twalker/3x5_tractyl/case/antoni-gaudi-Ca la Rosa_enhanced.webp

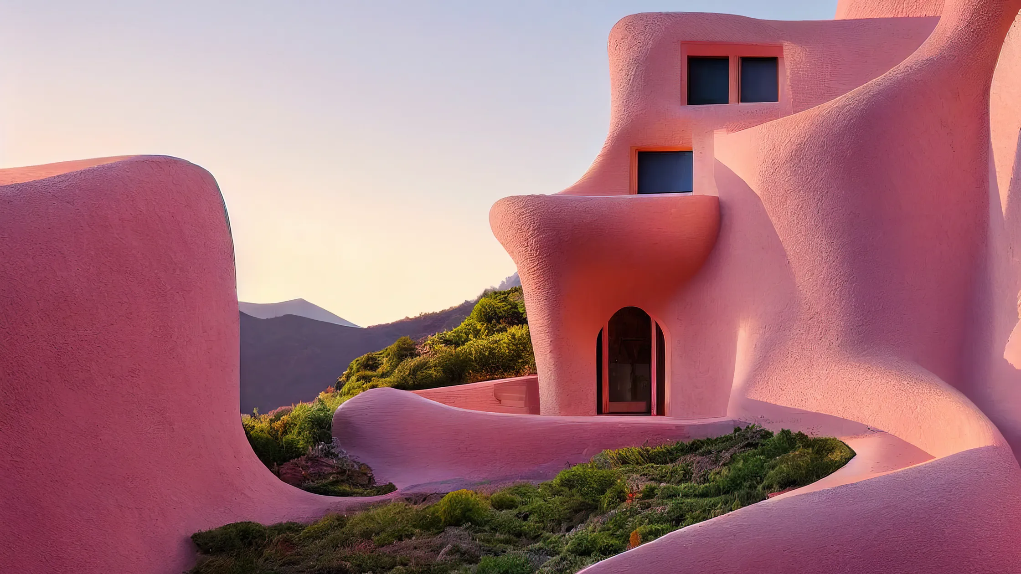
case/antoni-gaudi-Ca la Rosa_enhanced.webp
