twalker/3x5_tractyl/case/cosmos-design.png

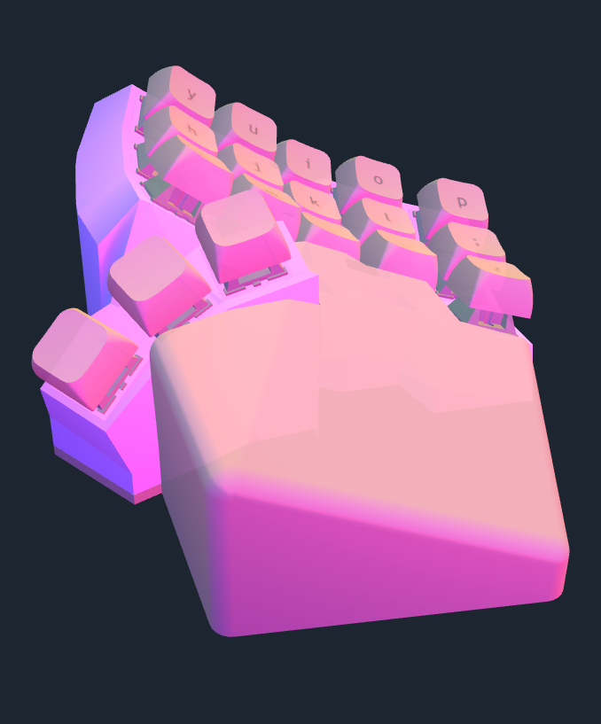
case/cosmos-design.png
