twalker/3x5_tractyl/case/orbital-in-slicer.png

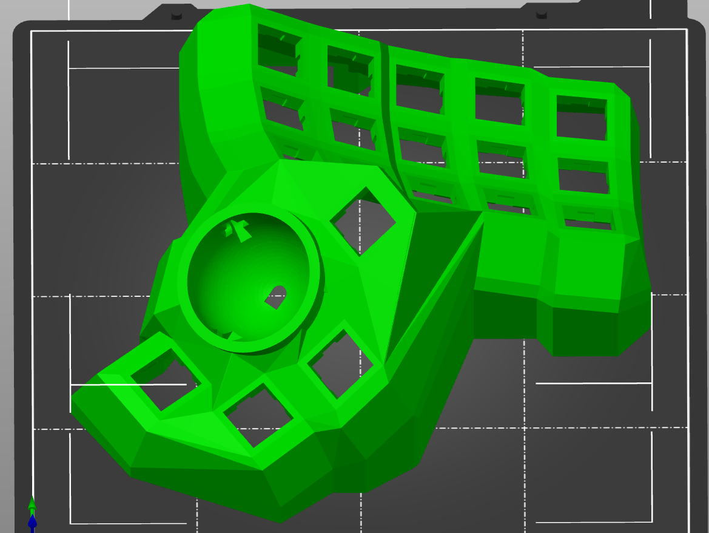
case/orbital-in-slicer.png
