twalker/3x5_tractyl/v2/3x5_tractyl-BothSidesRP2040_ce.png

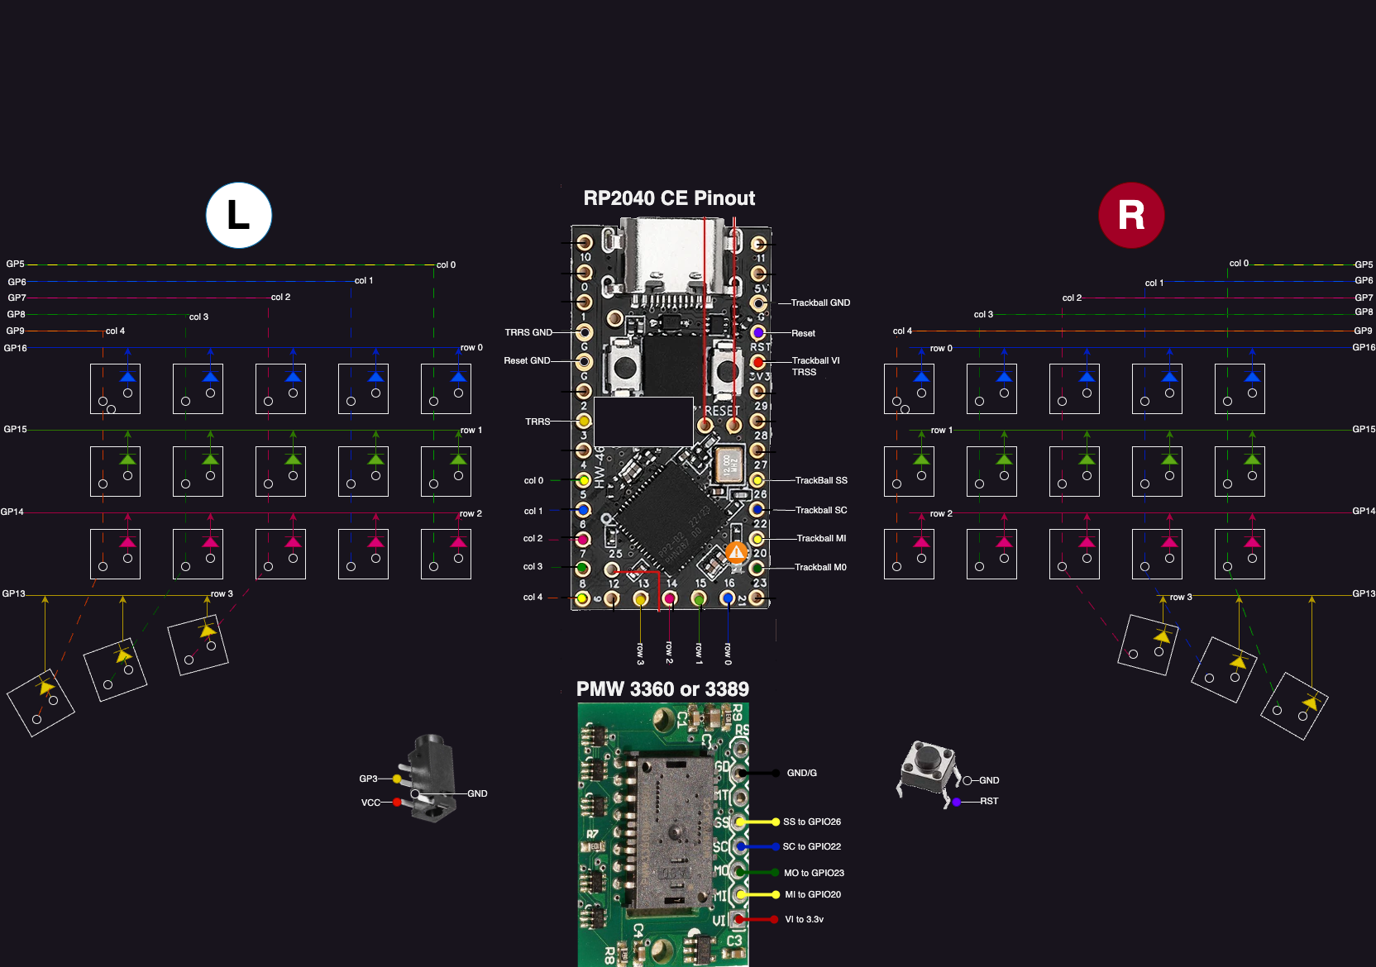
v2/3x5_tractyl-BothSidesRP2040_ce.png
