twalker/3x5_tractyl/v2/pmw3360_cleaned.jpg

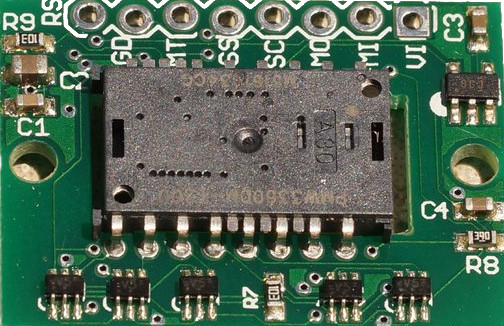
v2/pmw3360_cleaned.jpg
