twalker/3x5_tractyl/v2/Pro-Micro-RP2040-Mini-Development-Board-Dual-Core-Development-Board-Supports-Raspberry-Pi-Pico-MicroPython-4MB.jpg_.webp

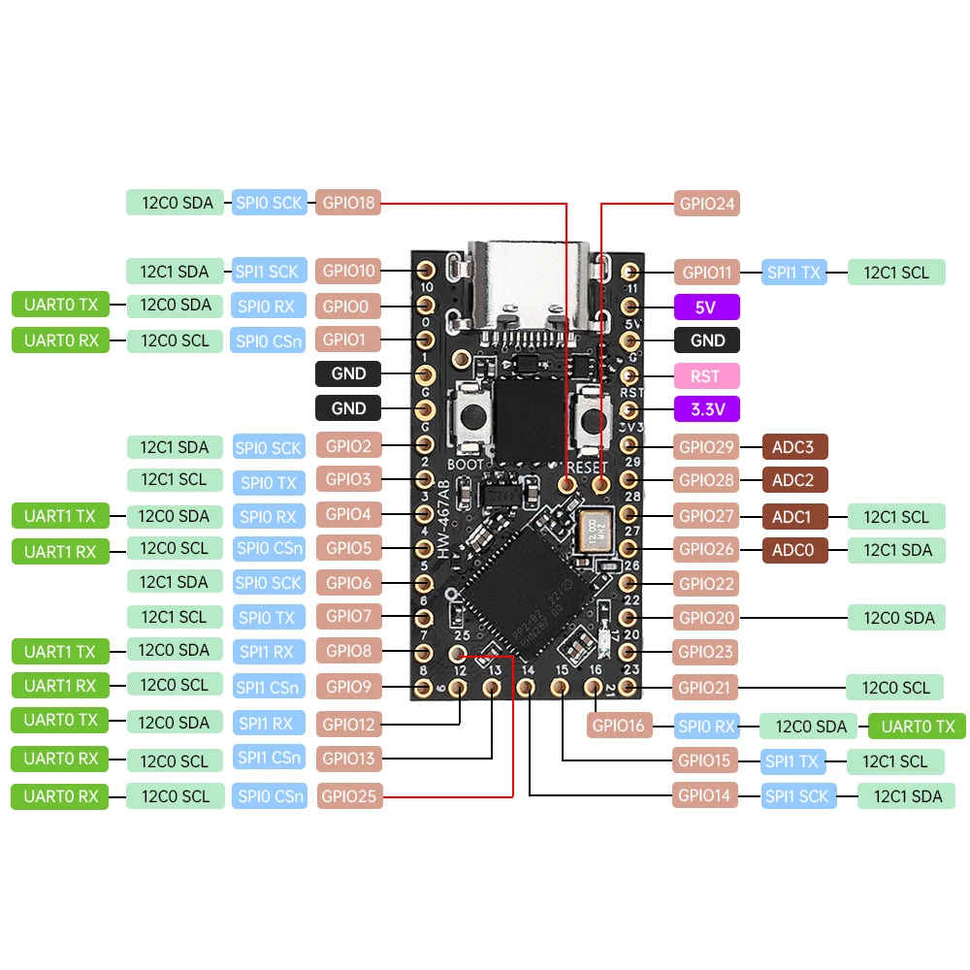
v2/Pro-Micro-RP2040-Mini-Development-Board-Dual-Core-Development-Board-Supports-Raspberry-Pi-Pico-MicroPython-4MB.jpg_.webp
