twalker/3x5_tractyl/v2/rp2040_ce.png

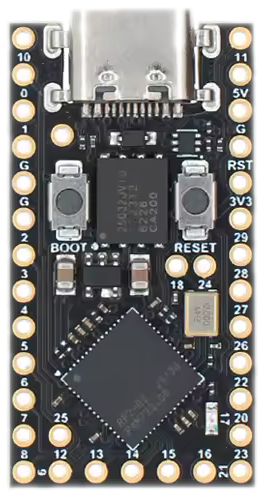
v2/rp2040_ce.png
