twalker/3x5_tractyl/v2/SpiralGalaxySKPCB.png

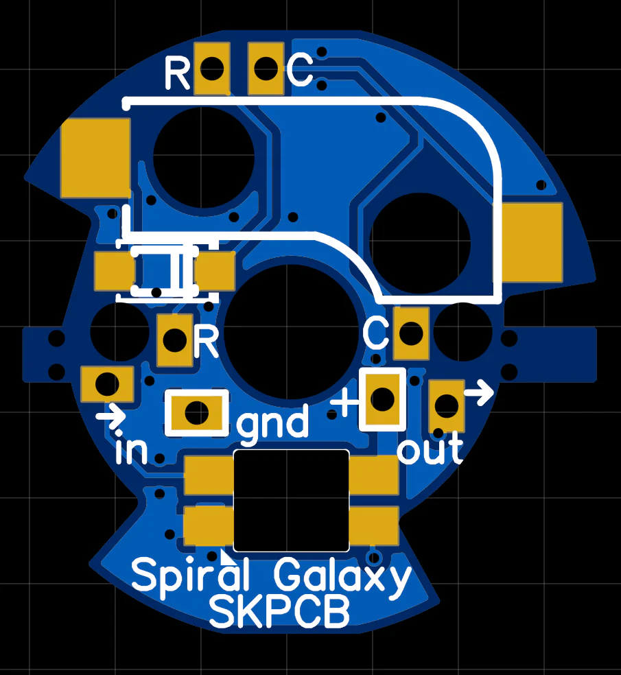
v2/SpiralGalaxySKPCB.png
