twalker/3x5_tractyl/v2_wireless/oled-positioning.png

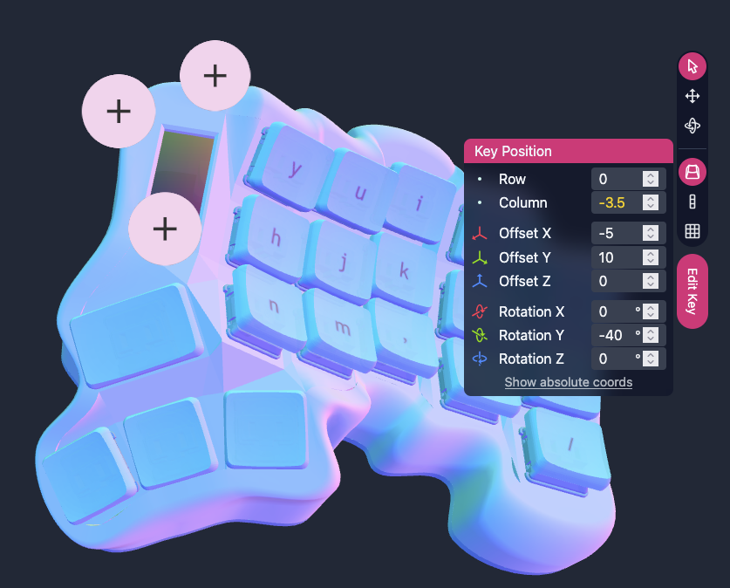
v2_wireless/oled-positioning.png
