twalker/3x5_tractyl/wiring-diagram/Elite-Pi_Pinout-Both-cleaned.png

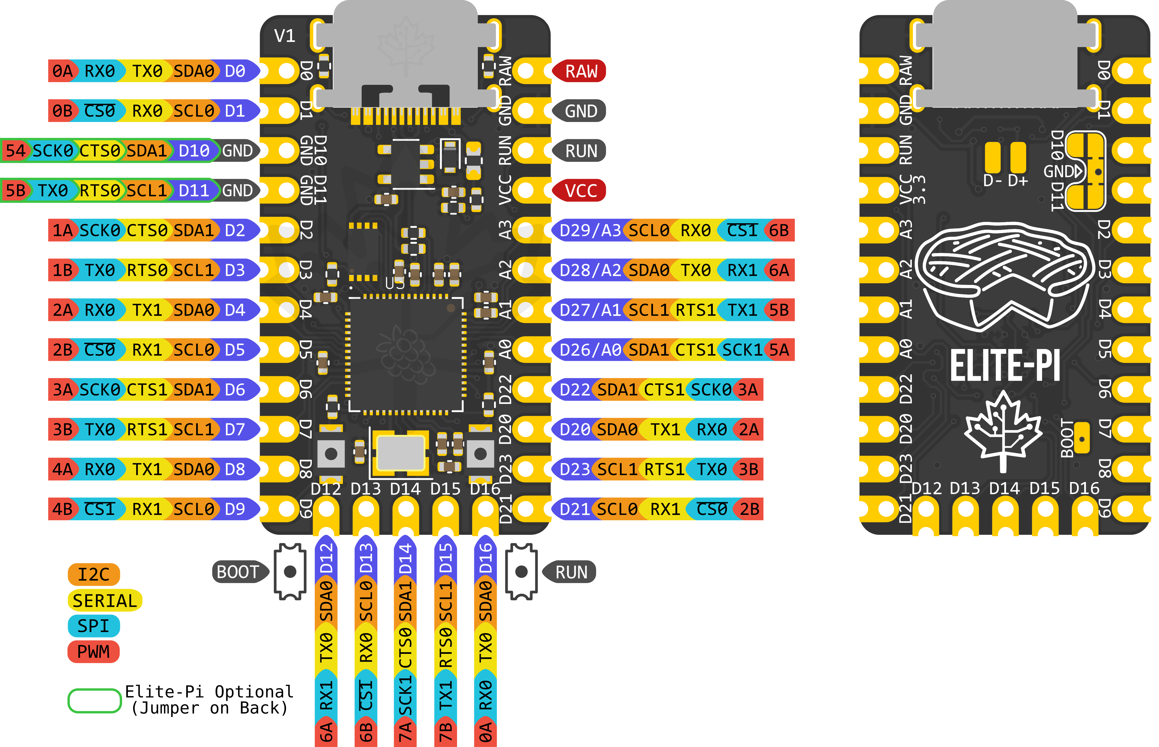
wiring-diagram/Elite-Pi_Pinout-Both-cleaned.png
