twalker/3x5_tractyl/wiring-diagram/Elite-Pi_Pinout-Top.png

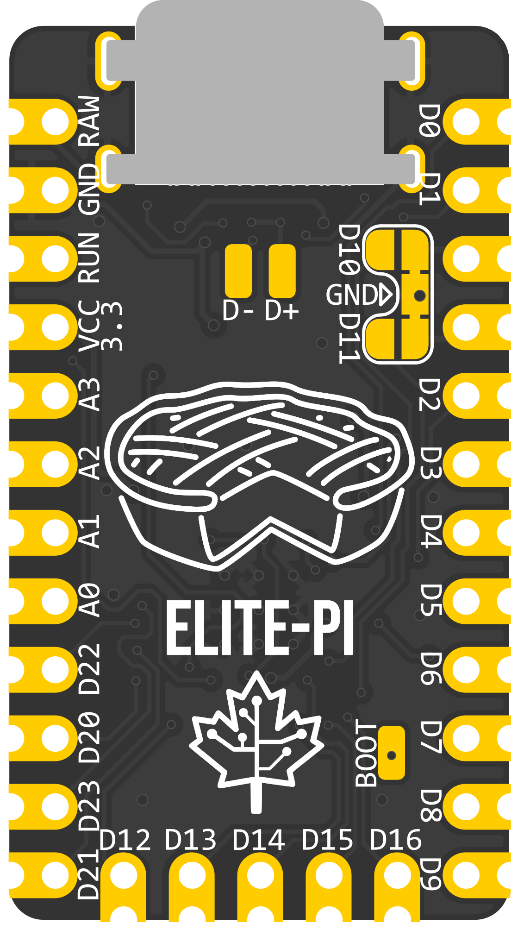
wiring-diagram/Elite-Pi_Pinout-Top.png
