twalker/3x5_tractyl/wiring-diagram/nice-view-pinout_cleaned.png

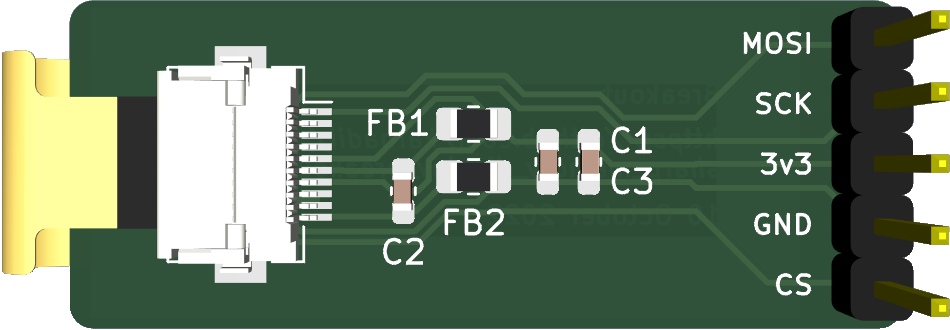
wiring-diagram/nice-view-pinout_cleaned.png
