twalker/3x5_tractyl/wiring-diagram/nice_nano_pinout-v2.png

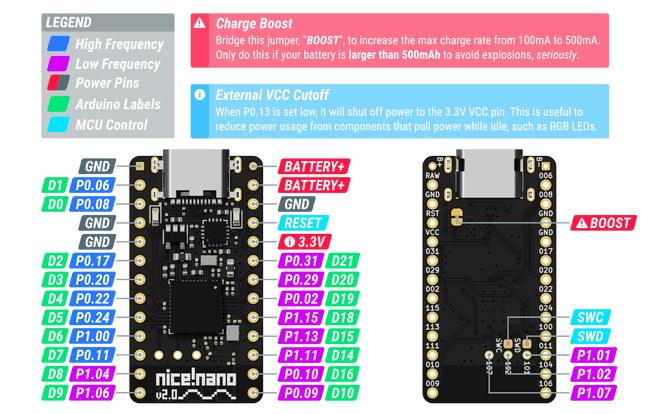
wiring-diagram/nice_nano_pinout-v2.png
