twalker/3x5_tractyl/wiring-diagram/pinout-advice.png

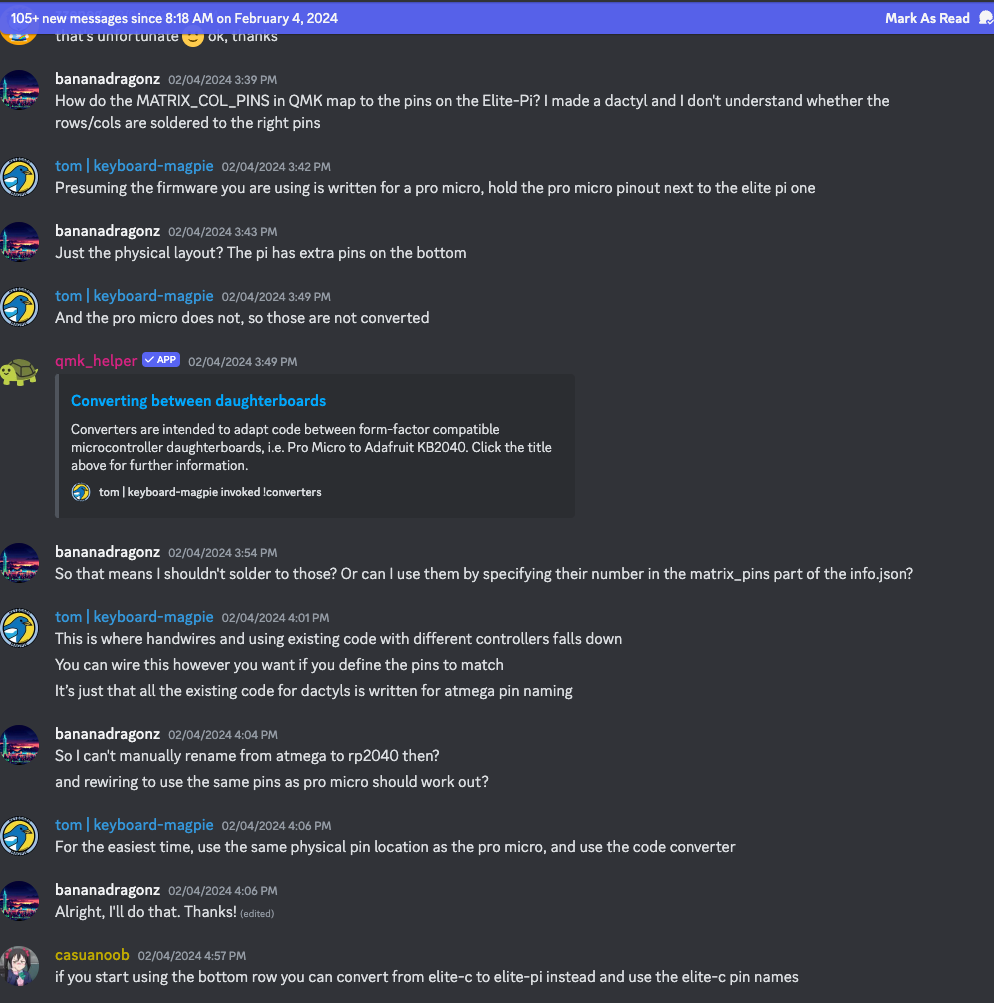
wiring-diagram/pinout-advice.png
