twalker/3x5_tractyl/wiring-diagram/promicro-pinout.png

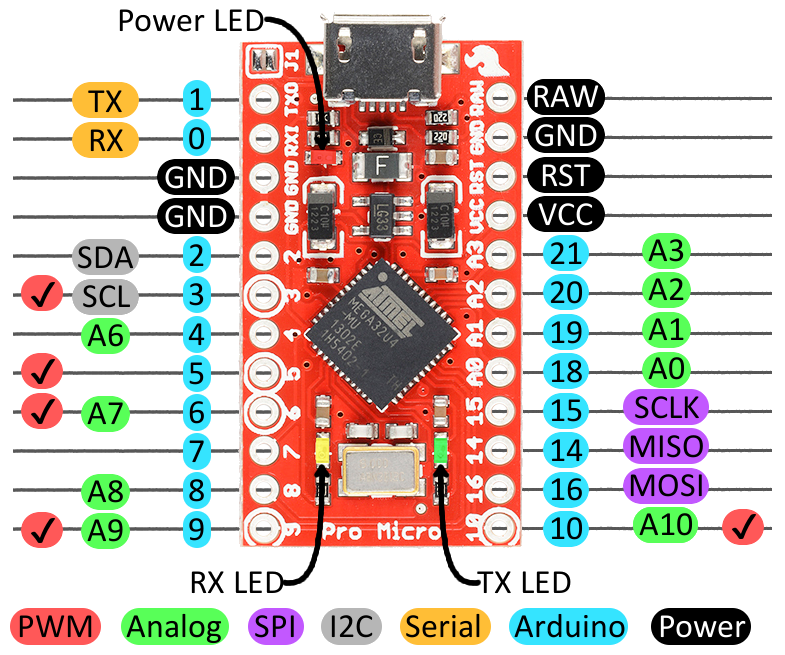
wiring-diagram/promicro-pinout.png
