twalker/3x5_tractyl/wiring-diagram/supermini-nrf52840-a-6-nice-nano-2-0-compatible-mcu-pinout.png

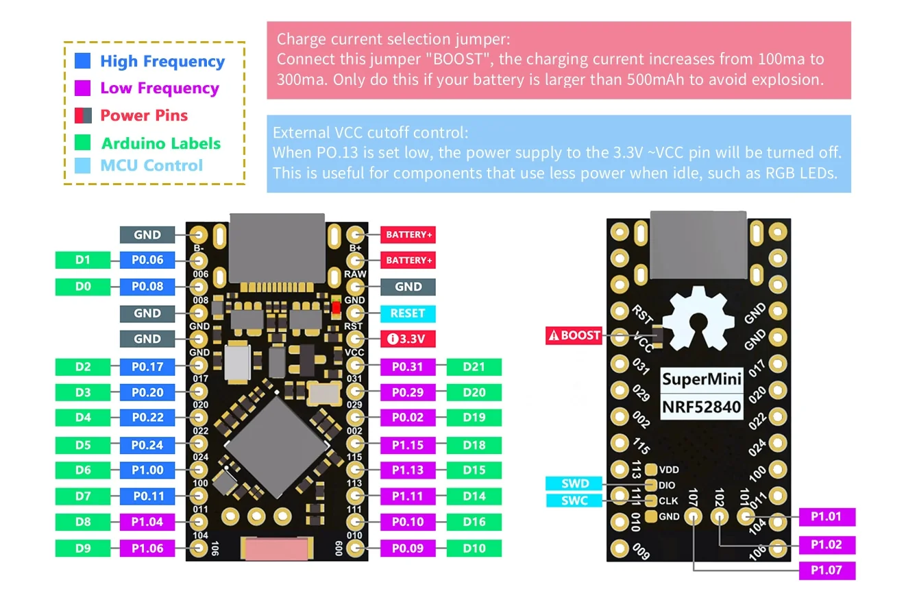
wiring-diagram/supermini-nrf52840-a-6-nice-nano-2-0-compatible-mcu-pinout.png
