twalker/3x5_tractyl/bill-of-materials.png

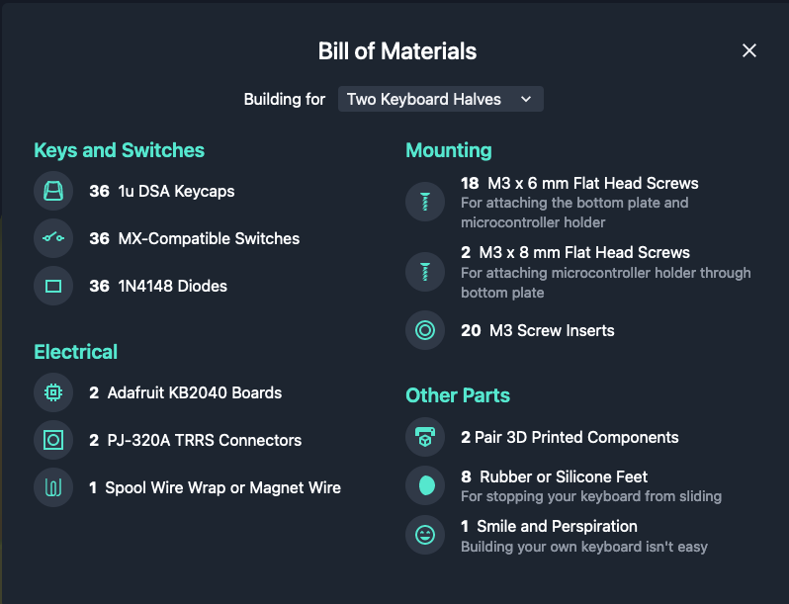
bill-of-materials.png
