twalker/3x5_tractyl/luca/luca_v2_hs_sm/luca_v2_hs_sm-plateright.stl

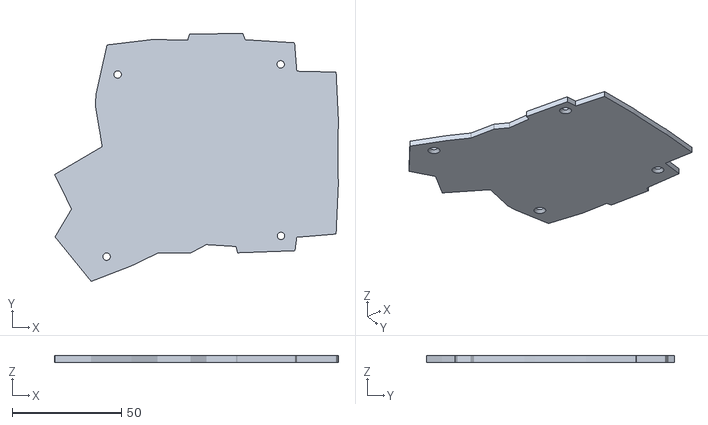
[picture p36: CAD file, 2026-05-09]
luca/luca_v2_hs_sm/luca_v2_hs_sm-plateright.stl
130.2 x 113.6 x 3.00
