twalker/3x5_tractyl/luca_v2.1_hs/luca_v2.1_hs_lg-holderright.stl

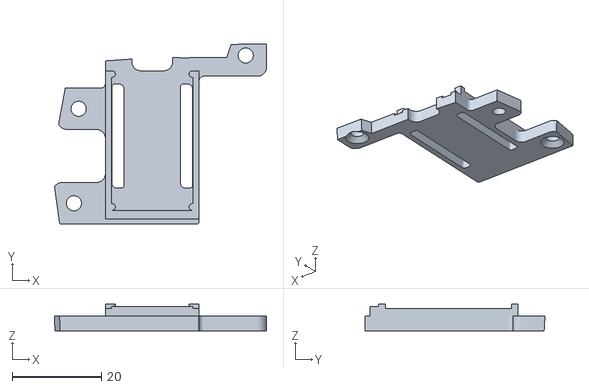
[picture p37: CAD file, 2026-05-09]
luca_v2.1_hs/luca_v2.1_hs_lg-holderright.stl
47.5 x 40.4 x 5.97
