twalker/3x5_tractyl/v2/cosmotylmt3v1-plateleft.stl

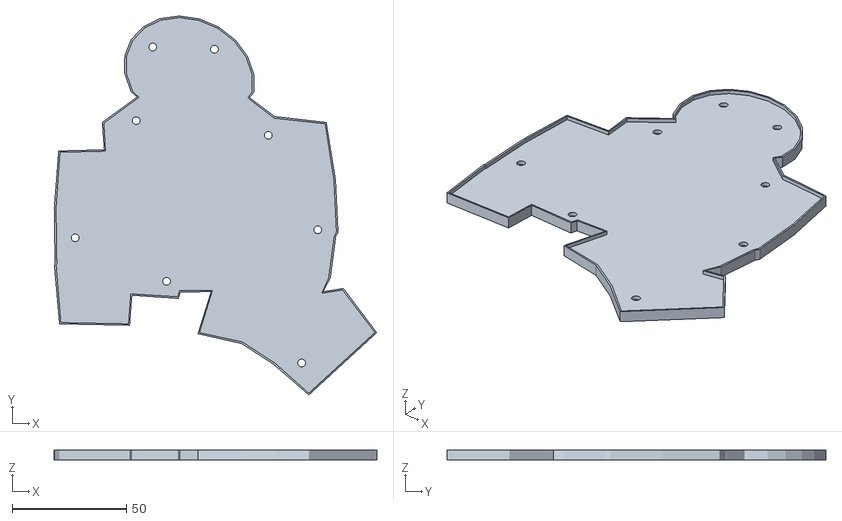
[picture p38: CAD file, 2024-12-28]
v2/cosmotylmt3v1-plateleft.stl
141.1 x 165.9 x 4.52
