twalker/3x5_tractyl/v2/costmos_choc_hotswap_v2/cosmos_choc_hotwap_v2.2-plateleft.stl

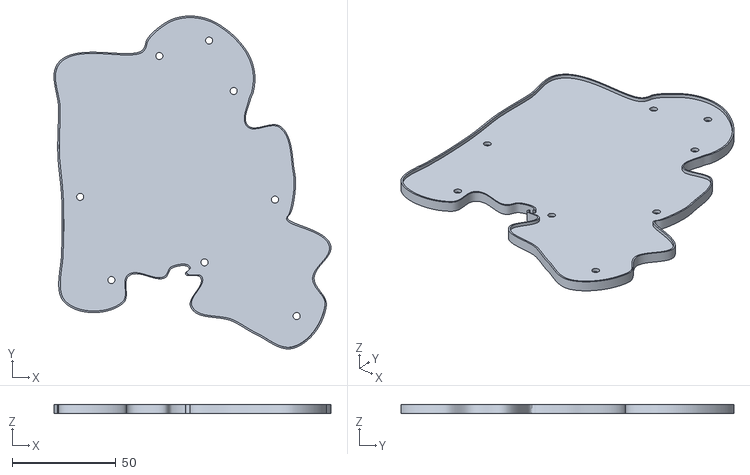
[picture p39: CAD file, 2024-12-28]
v2/costmos_choc_hotswap_v2/cosmos_choc_hotwap_v2.2-plateleft.stl
133.4 x 160.3 x 4.50
