twalker/3x5_tractyl/v2_wireless/cosmos_choc_hotwap_wireless_v2.5-holderright.stl

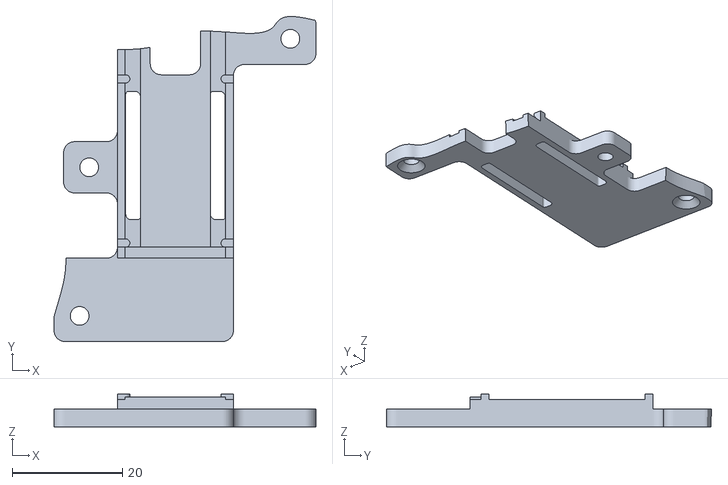
[picture p40: CAD file, 2025-02-22]
v2_wireless/cosmos_choc_hotwap_wireless_v2.5-holderright.stl
47.5 x 58.9 x 5.97
