twalker/3x5_tractyl/wireless_thumb_v1/v1.4/clemenza-thumb_v1.4-plateleft.stl

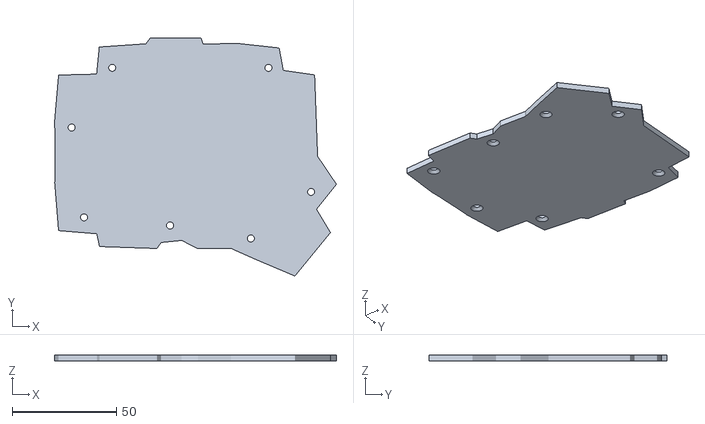
[picture p41: CAD file, 2026-05-09]
wireless_thumb_v1/v1.4/clemenza-thumb_v1.4-plateleft.stl
135.5 x 114.4 x 3.00
