twalker/3x5_tractyl/case/lowprocosmotyl2-noweb3-wristrest-longer.3mf

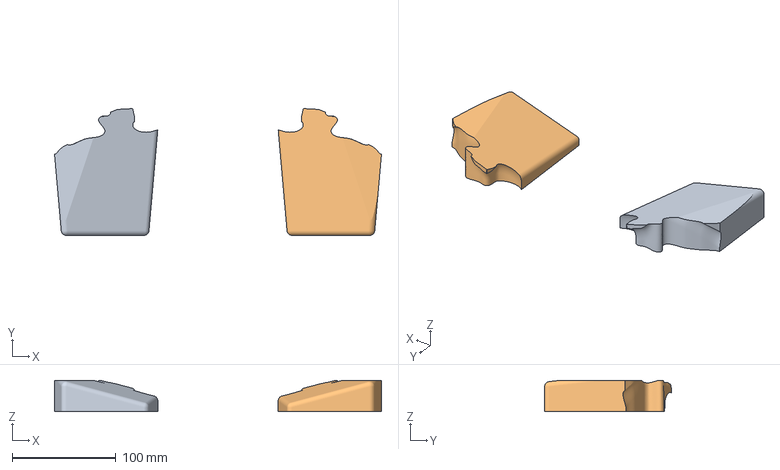
[picture p42: CAD file, 2024-06-30]
case/lowprocosmotyl2-noweb3-wristrest-longer.3mf
315.6 x 122.4 x 30.2 mm
lowprocosmotyl2-noweb3-wristrest-right.stl
lowprocosmotyl2-noweb3-wristrest-left.stl
