twalker/3x5_tractyl/clemenza-plus/clemenza-plus_v1-plateleft.stl

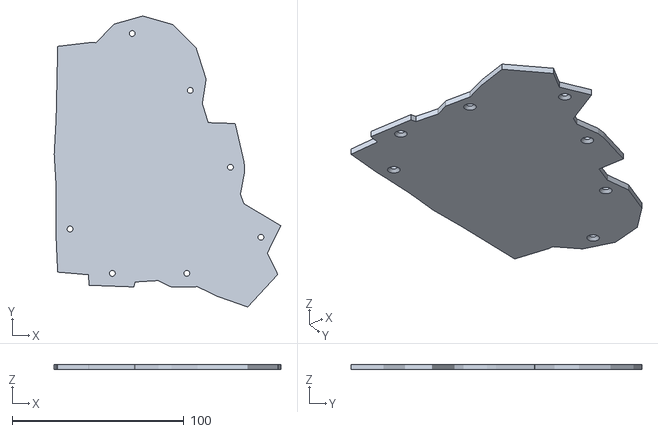
[picture p43: CAD file, 2026-05-09]
clemenza-plus/clemenza-plus_v1-plateleft.stl
132.1 x 169.6 x 3.00
