twalker/3x5_tractyl/luca/luca_v2_hs_lg/luca_v2_hs_lg.3mf

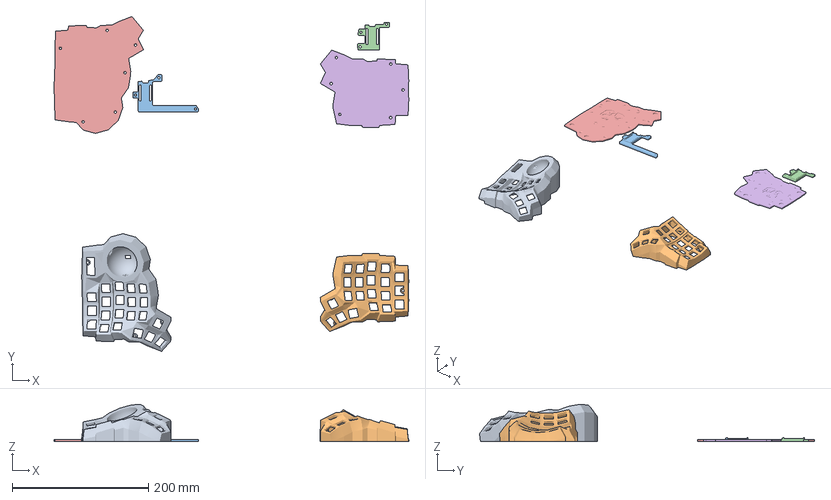
[picture p44: CAD file, 2026-05-09]
luca/luca_v2_hs_lg/luca_v2_hs_lg.3mf
521.2 x 492.3 x 54.9 mm
luca_v2_hs_lg-caseleft.stl
luca_v2_hs_lg-caseright.stl
luca_v2_hs_lg-holderleft.stl
luca_v2_hs_lg-holderright.stl
luca_v2_hs_lg-plateleft.stl
luca_v2_hs_lg-plateright.stl
