twalker/3x5_tractyl/luca/luca_v2_hs_sm/luca_v2_hs_sm-plateleft.stl

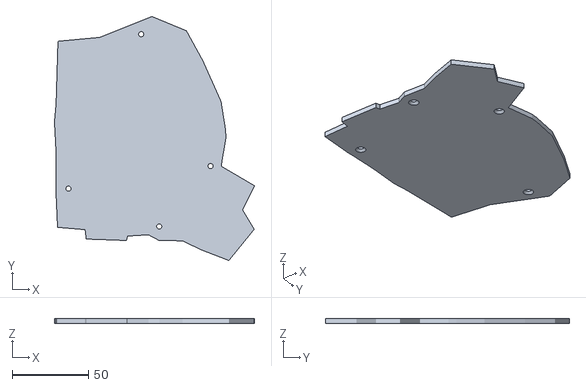
[picture p45: CAD file, 2026-05-09]
luca/luca_v2_hs_sm/luca_v2_hs_sm-plateleft.stl
131.1 x 159.9 x 3.00
