twalker/3x5_tractyl/v2/cosmos_choc_hotwap_v2.41/cosmos_choc_hotwap_v2.41-holderright.stl

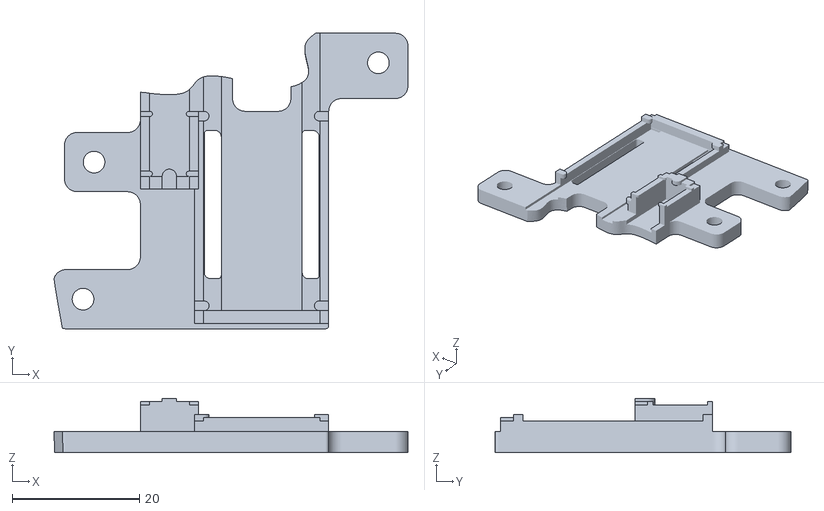
[picture p46: CAD file, 2025-01-20]
v2/cosmos_choc_hotwap_v2.41/cosmos_choc_hotwap_v2.41-holderright.stl
55.6 x 46.4 x 8.50
