twalker/3x5_tractyl/v2/cosmoskreedes_v1-holderleft.stl

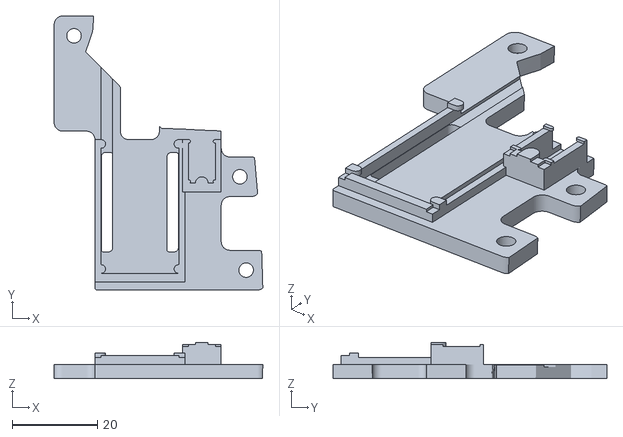
[picture p47: CAD file, 2024-12-28]
v2/cosmoskreedes_v1-holderleft.stl
48.9 x 64.1 x 8.50
