twalker/3x5_tractyl/v2/costmos_choc_hotswap_v2/cosmos_choc_hotwap_v2.2-holderleft.stl

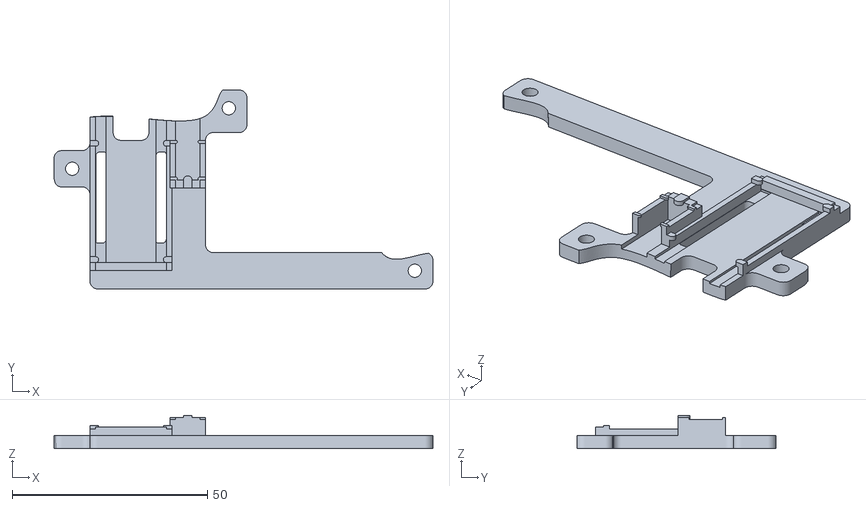
[picture p48: CAD file, 2024-12-28]
v2/costmos_choc_hotswap_v2/cosmos_choc_hotwap_v2.2-holderleft.stl
97.0 x 50.9 x 8.50
