twalker/3x5_tractyl/v2_wireless/cosmos_choc_hotwap_wireless_v2.5-holderleft.stl

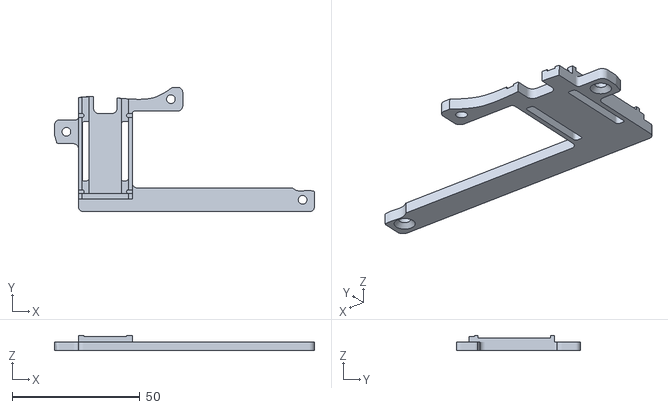
[picture p49: CAD file, 2025-02-22]
v2_wireless/cosmos_choc_hotwap_wireless_v2.5-holderleft.stl
101.6 x 48.6 x 5.97
