twalker/3x5_tractyl/case/lowprocosmotyl2-noweb-wristrests.3mf

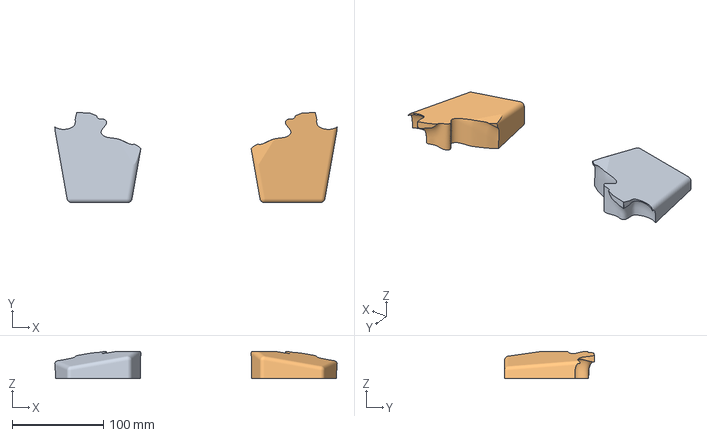
[picture p51: CAD file, 2024-06-30]
case/lowprocosmotyl2-noweb-wristrests.3mf
310.7 x 99.1 x 30.2 mm
lowprocosmotyl2-noweb-wristrest-left.stl
lowprocosmotyl2-noweb-wristrest-right.stl
