twalker/3x5_tractyl/clemenza-plus/clemenza-plus_v1-caseleft.stl

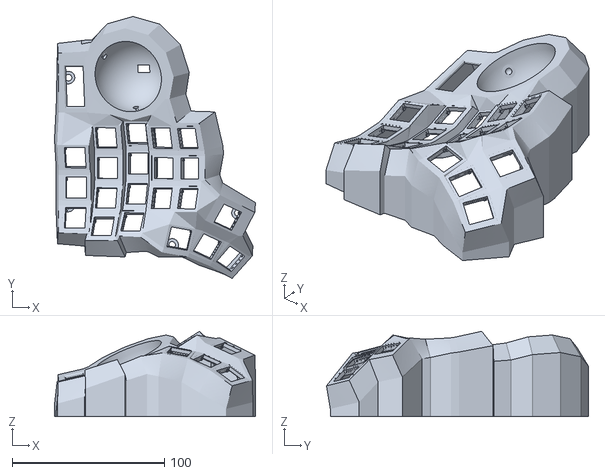
[picture p52: CAD file, 2026-05-09]
clemenza-plus/clemenza-plus_v1-caseleft.stl
132.1 x 172.1 x 56.1
