twalker/3x5_tractyl/luca/luca_v1.5-casetest.stl

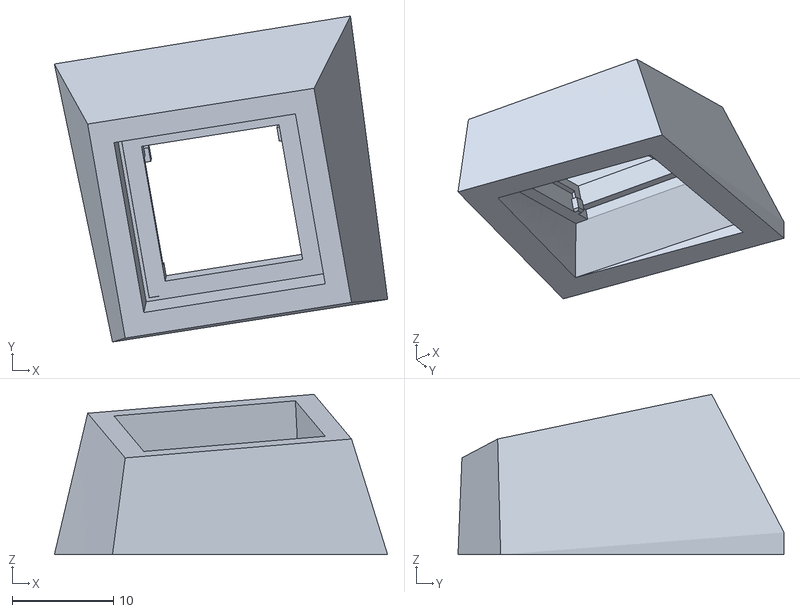
[picture p53: CAD file, 2026-05-09]
luca/luca_v1.5-casetest.stl
32.9 x 32.2 x 15.8
