twalker/3x5_tractyl/luca/luca_v2_hs_sm/luca_v2_hs_sm-caseright.stl

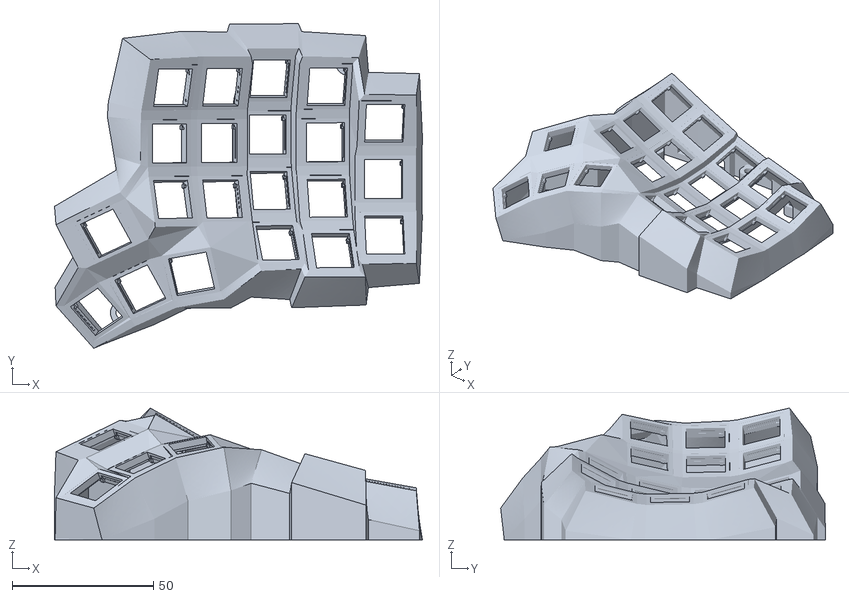
[picture p54: CAD file, 2026-05-09]
luca/luca_v2_hs_sm/luca_v2_hs_sm-caseright.stl
130.2 x 114.9 x 46.6
