twalker/3x5_tractyl/v2/cosmotylmt3v1-holderleft.stl

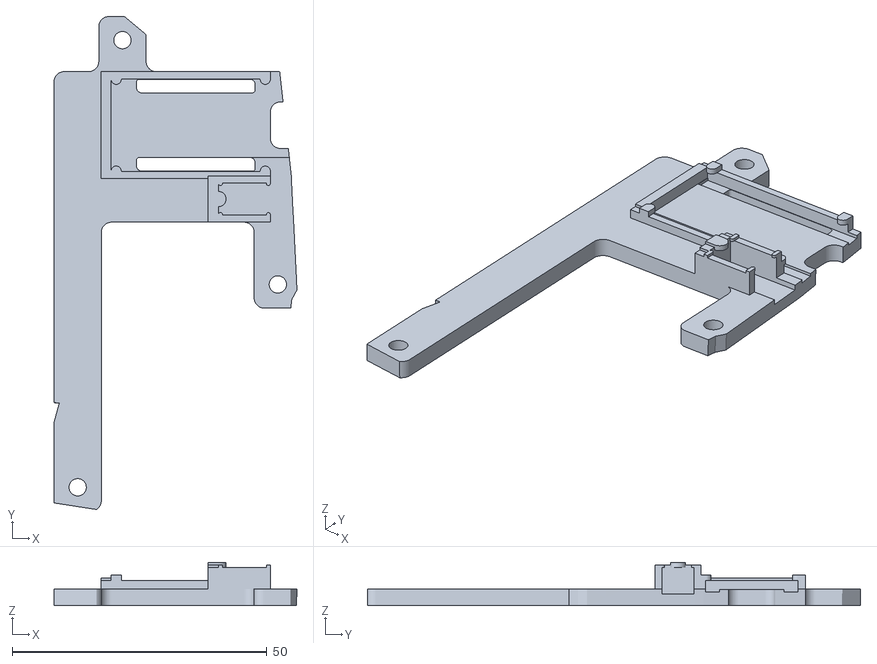
[picture p55: CAD file, 2024-12-28]
v2/cosmotylmt3v1-holderleft.stl
47.7 x 96.8 x 8.50
