twalker/3x5_tractyl/v2/costmos_choc_hotswap_v2/cosmos_choc_hotwap_v2.2-holderright.stl

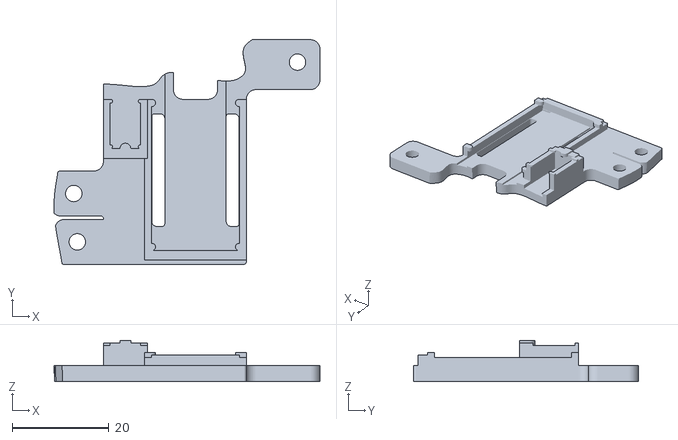
[picture p56: CAD file, 2024-12-28]
v2/costmos_choc_hotswap_v2/cosmos_choc_hotwap_v2.2-holderright.stl
55.0 x 46.5 x 8.50
