twalker/3x5_tractyl/v2_wireless/cosmos_choc_hotwap_wireless_v2.5-plateleft.stl

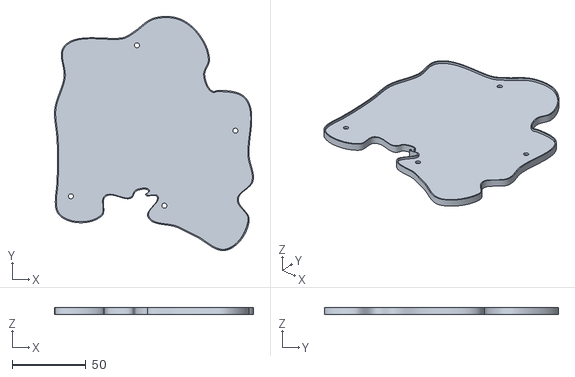
[picture p57: CAD file, 2025-02-22]
v2_wireless/cosmos_choc_hotwap_wireless_v2.5-plateleft.stl
134.6 x 158.4 x 4.50
