twalker/3x5_tractyl/wireless_thumb_v1/v1.4/clemenza-thumb_v1.4-plateright.stl

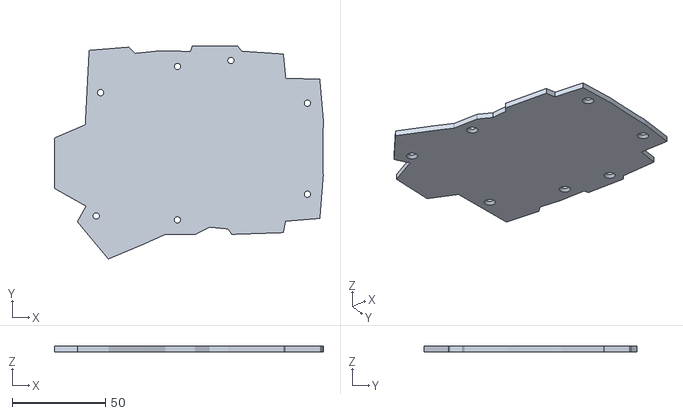
[picture p58: CAD file, 2026-05-09]
wireless_thumb_v1/v1.4/clemenza-thumb_v1.4-plateright.stl
144.4 x 114.4 x 3.00
