twalker/3x5_tractyl/case/lowprocosmotyl2-wristrest-left.stl

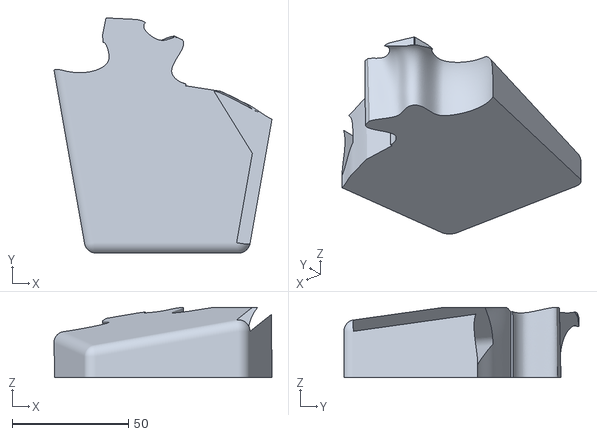
[picture p59: CAD file, 2024-06-30]
case/lowprocosmotyl2-wristrest-left.stl
93.6 x 101.0 x 30.2
