twalker/3x5_tractyl/clemenza-plus/clemenza-plus_v1.3mf

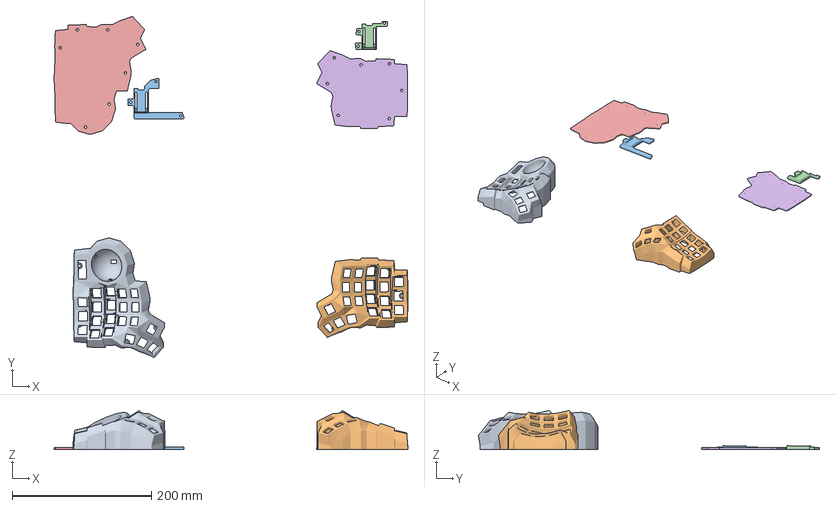
[picture p60: CAD file, 2026-05-09]
clemenza-plus/clemenza-plus_v1.3mf
508.7 x 490.3 x 56.1 mm
clemenza-plus_v1-caseleft.stl
clemenza-plus_v1-caseright.stl
clemenza-plus_v1-holderleft.stl
clemenza-plus_v1-holderright.stl
clemenza-plus_v1-plateleft.stl
clemenza-plus_v1-plateright.stl
