twalker/3x5_tractyl/luca/luca_v2_hs_sm/luca_v2_hs_sm-caseleft.stl

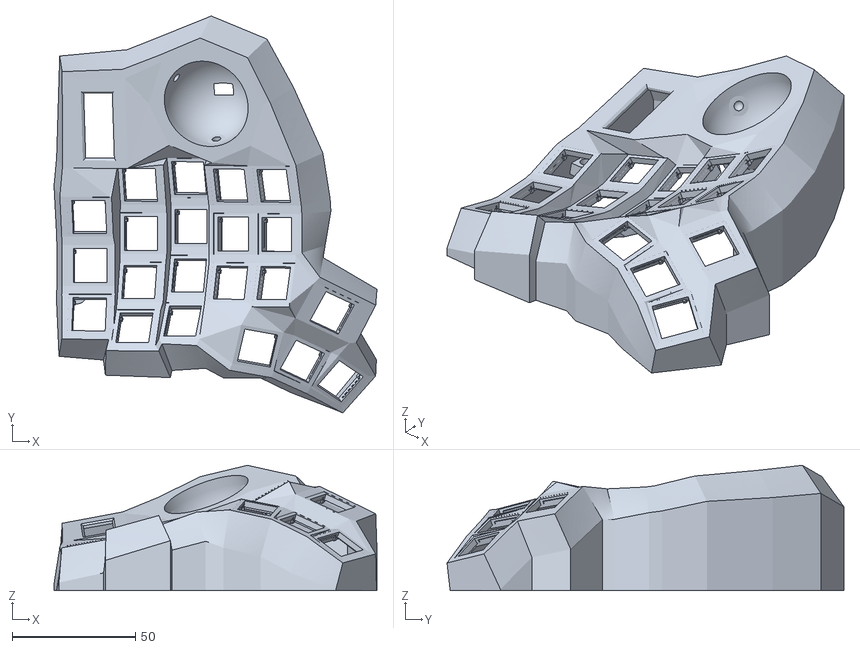
[picture p61: CAD file, 2026-05-09]
luca/luca_v2_hs_sm/luca_v2_hs_sm-caseleft.stl
131.1 x 161.2 x 50.9
