twalker/3x5_tractyl/v2/cosmoskreedes_v1-plateright.stl

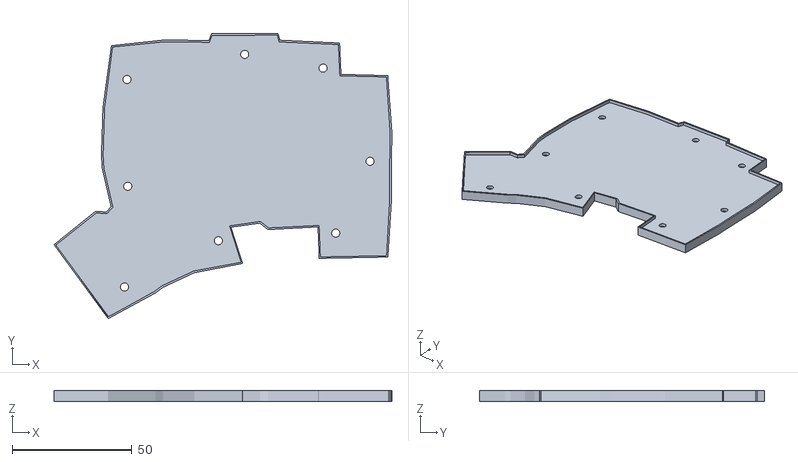
[picture p62: CAD file, 2024-12-28]
v2/cosmoskreedes_v1-plateright.stl
140.9 x 118.9 x 4.50
