twalker/3x5_tractyl/wireless_thumb_v1/v1.4/clemenza-thumb_v1.4-holderleft.stl

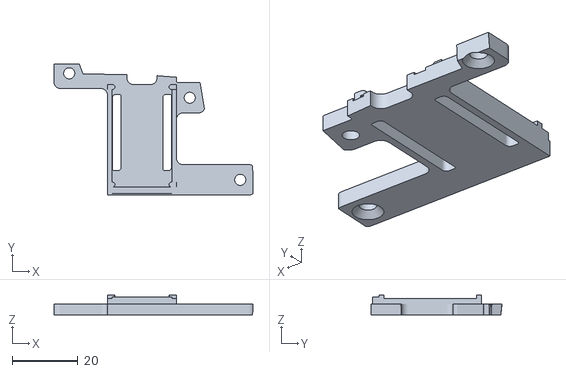
[picture p63: CAD file, 2026-05-09]
wireless_thumb_v1/v1.4/clemenza-thumb_v1.4-holderleft.stl
60.7 x 40.0 x 5.97
