twalker/3x5_tractyl/case/lowprocosmotyl2-holder-left.stl

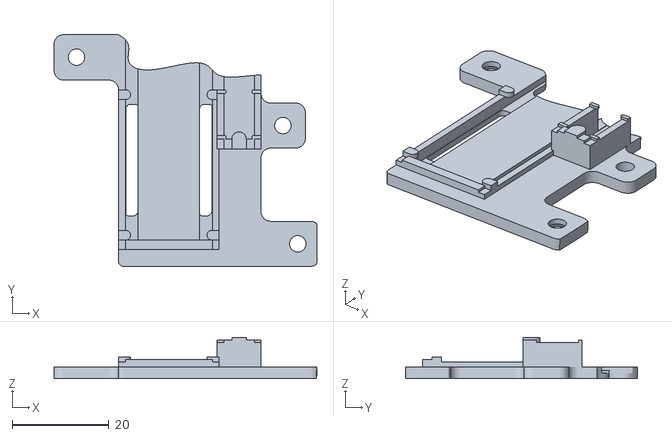
[picture p64: CAD file, 2024-06-30]
case/lowprocosmotyl2-holder-left.stl
54.3 x 47.8 x 8.50
