twalker/3x5_tractyl/luca/luca_v2_hs_lg/luca_v2_hs_lg-plateright.stl

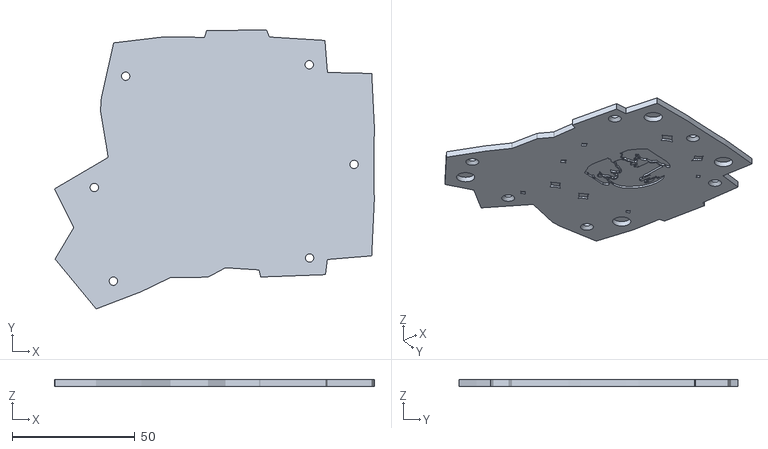
[picture p65: CAD file, 2026-05-09]
luca/luca_v2_hs_lg/luca_v2_hs_lg-plateright.stl
130.2 x 113.5 x 3.00
