twalker/3x5_tractyl/luca/luca_v2_hs_sm/luca_v2_hs_sm-holderright.stl

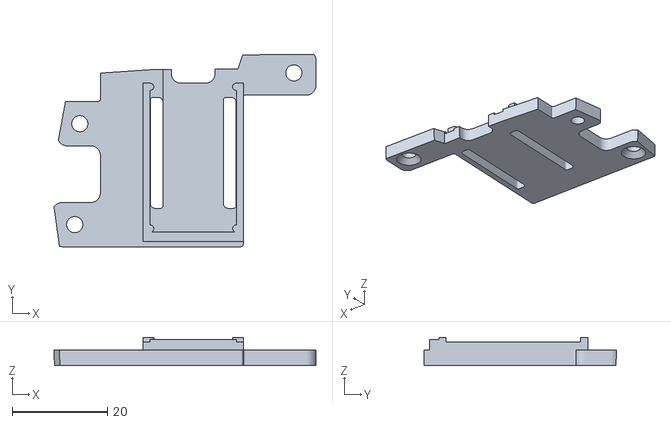
[picture p66: CAD file, 2026-05-09]
luca/luca_v2_hs_sm/luca_v2_hs_sm-holderright.stl
55.0 x 40.4 x 5.97
