twalker/3x5_tractyl/luca_v2.1_hs/luca_v2.1_hs_lg-caseright.stl

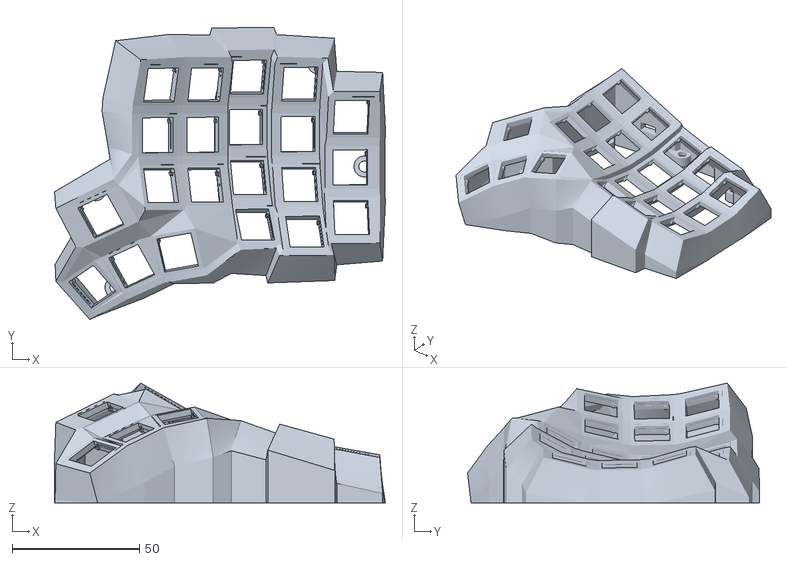
[picture p67: CAD file, 2026-05-09]
luca_v2.1_hs/luca_v2.1_hs_lg-caseright.stl
130.2 x 114.9 x 47.1
