twalker/3x5_tractyl/v2/cosmotylmt3v1-wristrestright.stl

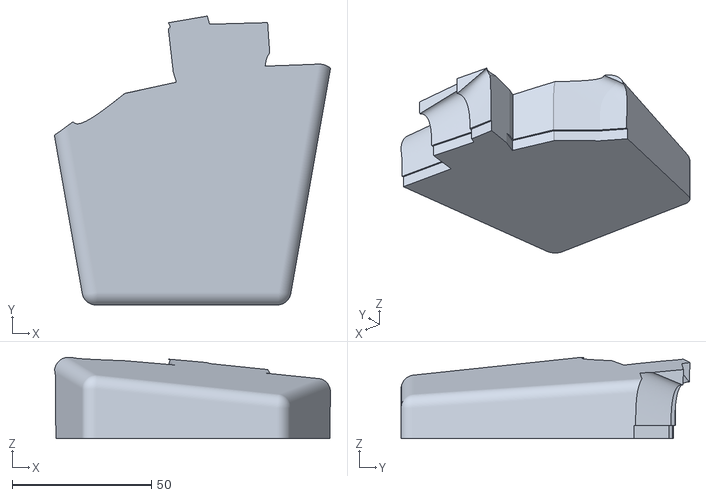
[picture p68: CAD file, 2024-12-28]
v2/cosmotylmt3v1-wristrestright.stl
99.2 x 103.9 x 29.1
