twalker/3x5_tractyl/wireless_thumb_v1/v1.4/clemenza-thumb_v1.4right.step

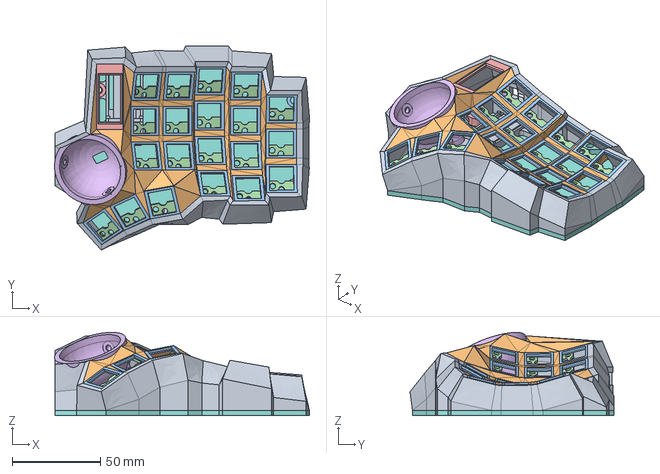
[picture p69: CAD file, 2026-05-09]
wireless_thumb_v1/v1.4/clemenza-thumb_v1.4right.step
144.7 x 115.8 x 47.2 mm
