twalker/3x5_tractyl/case/38mmTrackBallHolder.3mf

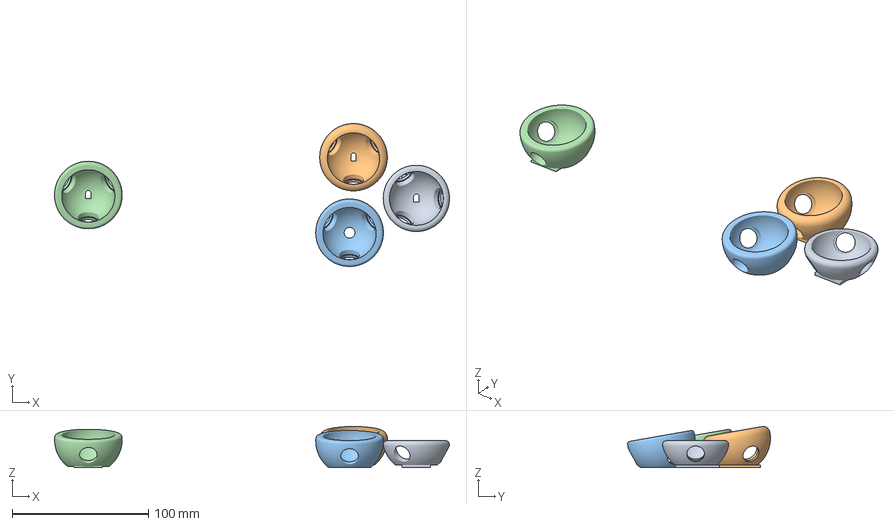
[picture p70: CAD file, 2024-06-30]
case/38mmTrackBallHolder.3mf
289.9 x 104.9 x 30.1 mm
38mmTrackBallHolder v15.stl
38mmTrackBallHolder v16.stl
Cup.stl
38mmTrackBallHolder v18.stl
