twalker/3x5_tractyl/clemenza-plus/clemenza-plus_v1-caseright.stl

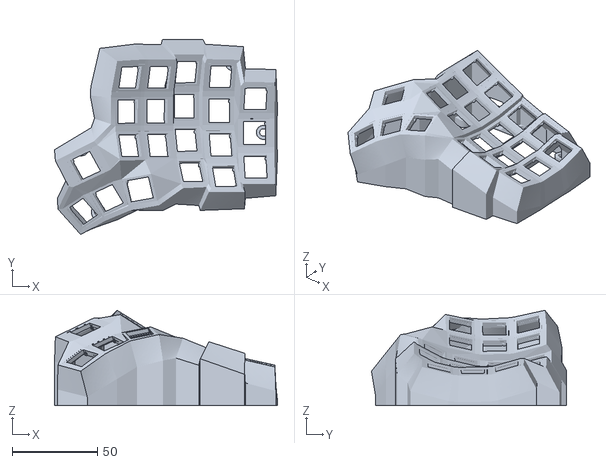
[picture p71: CAD file, 2026-05-09]
clemenza-plus/clemenza-plus_v1-caseright.stl
131.1 x 114.7 x 56.1
