twalker/3x5_tractyl/luca/luca_v2_hs_sm/luca_v2_hs_sm-holderleft.stl

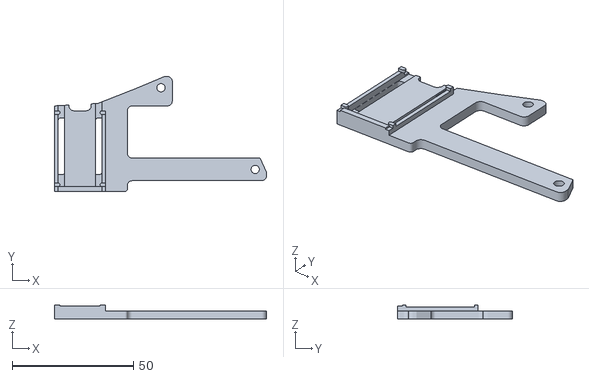
[picture p72: CAD file, 2026-05-09]
luca/luca_v2_hs_sm/luca_v2_hs_sm-holderleft.stl
87.3 x 47.4 x 5.97
