twalker/3x5_tractyl/wireless_thumb_v1/v1.4/clemenza-thumb_v1.4.3mf

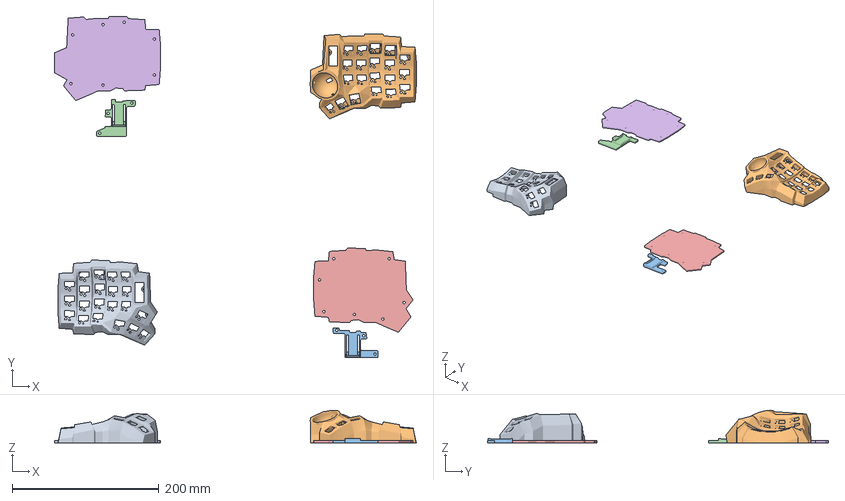
[picture p73: CAD file, 2026-05-09]
wireless_thumb_v1/v1.4/clemenza-thumb_v1.4.3mf
492.5 x 464.0 x 44.2 mm
clemenza-thumb_v1.4-caseleft.stl
clemenza-thumb_v1.4-caseright.stl
clemenza-thumb_v1.4-holderleft.stl
clemenza-thumb_v1.4-holderright.stl
clemenza-thumb_v1.4-plateleft.stl
clemenza-thumb_v1.4-plateright.stl
