twalker/3x5_tractyl/case/lowprocosmotyl2-noweb3-wristrest-left.stl

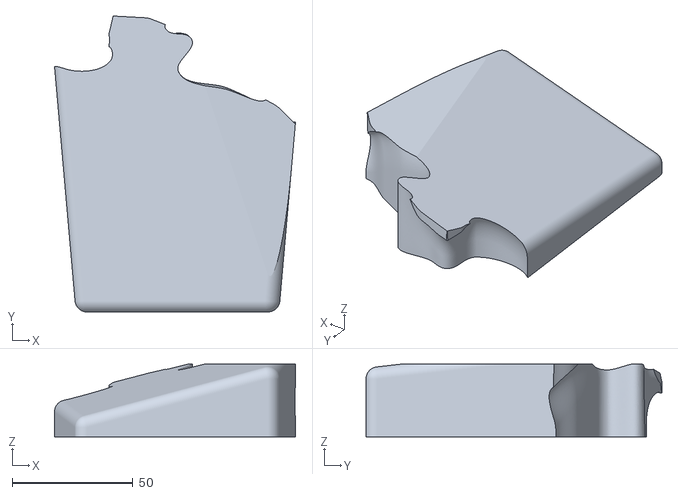
[picture p74: CAD file, 2024-06-30]
case/lowprocosmotyl2-noweb3-wristrest-left.stl
99.7 x 122.4 x 30.2
