twalker/3x5_tractyl/luca/luca_v2-plateleft.stl

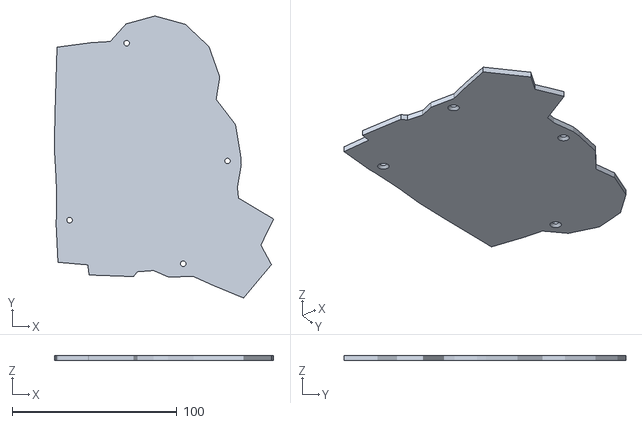
[picture p75: CAD file, 2026-05-09]
luca/luca_v2-plateleft.stl
133.0 x 171.1 x 3.00
