twalker/3x5_tractyl/v2/cosmoskreedes_v1-plateleft.stl

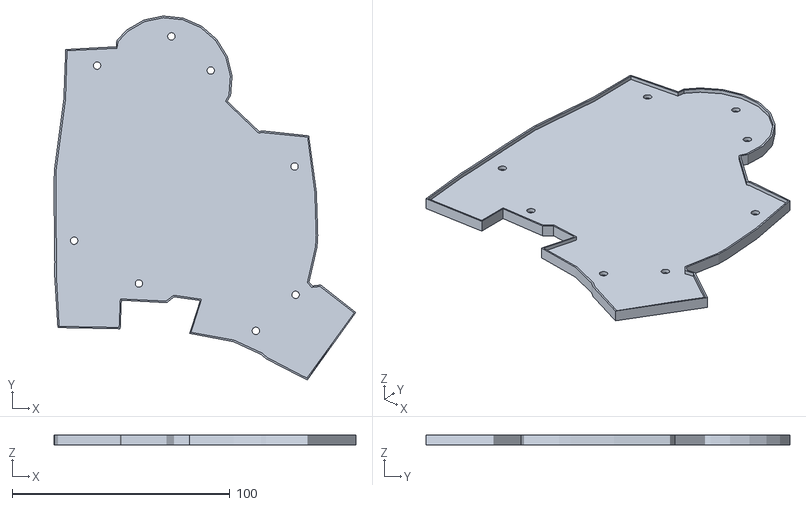
[picture p76: CAD file, 2024-12-28]
v2/cosmoskreedes_v1-plateleft.stl
138.6 x 167.3 x 4.52
