twalker/3x5_tractyl/wireless_thumb_v1/v1.4/clemenza-thumb_v1.4left.step

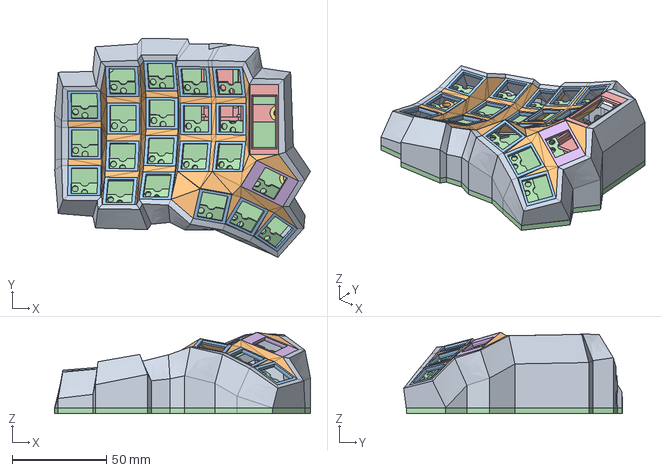
[picture p77: CAD file, 2026-05-09]
wireless_thumb_v1/v1.4/clemenza-thumb_v1.4left.step
135.5 x 115.8 x 43.1 mm
