twalker/3x5_tractyl/case/lowprocosmotyl2-noweb-parts.3mf

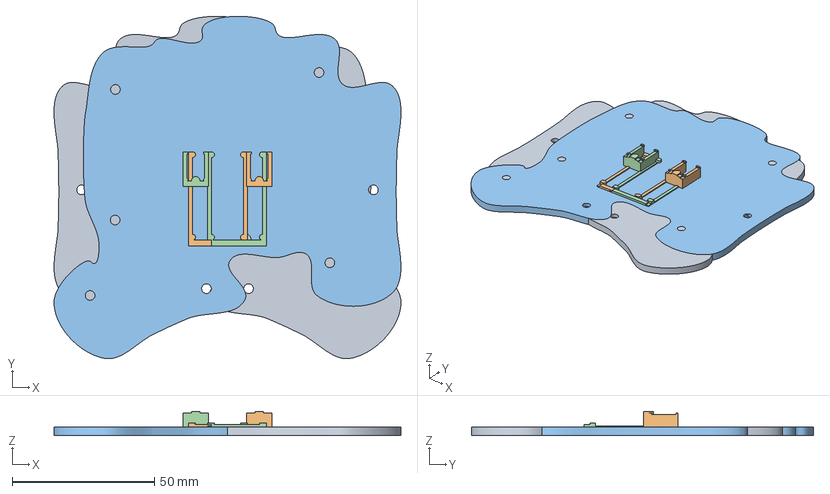
[picture p78: CAD file, 2024-06-30]
case/lowprocosmotyl2-noweb-parts.3mf
122.1 x 120.4 x 8.50 mm
lowprocosmotyl2-noweb-plate-left.stl
lowprocosmotyl2-noweb-holder-left.stl
lowprocosmotyl2-noweb-plate-right.stl
lowprocosmotyl2-noweb-holder-right.stl
