twalker/3x5_tractyl/v2/cosmos_choc_hotwap_v1.3mf

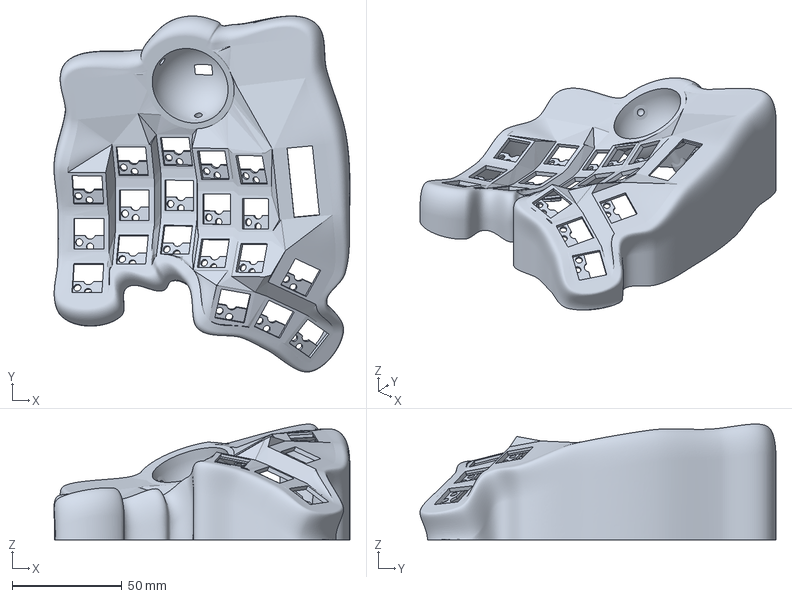
[picture p79: CAD file, 2024-12-28]
v2/cosmos_choc_hotwap_v1.3mf
134.8 x 162.2 x 52.8 mm
