twalker/3x5_tractyl/luca/luca_v2-holderright.stl

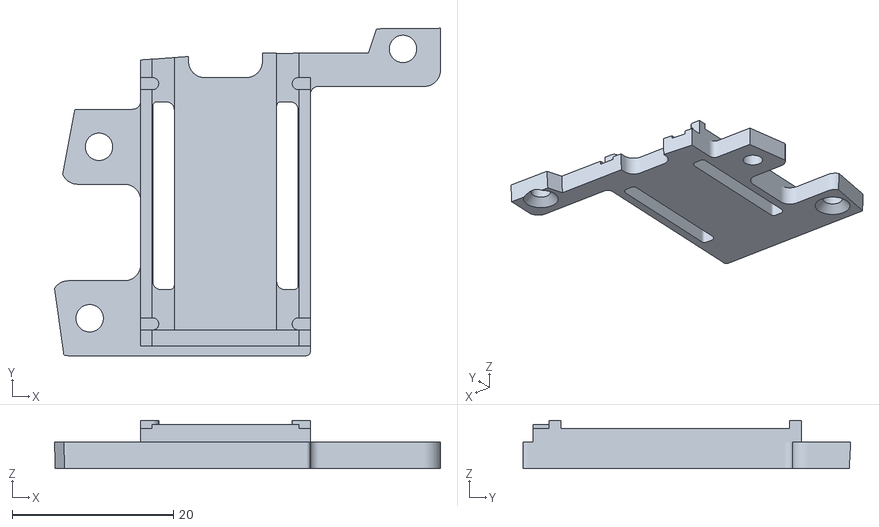
[picture p81: CAD file, 2026-05-09]
luca/luca_v2-holderright.stl
47.9 x 40.6 x 5.97
