twalker/3x5_tractyl/v2/cosmotylmt3v1-holderright.stl

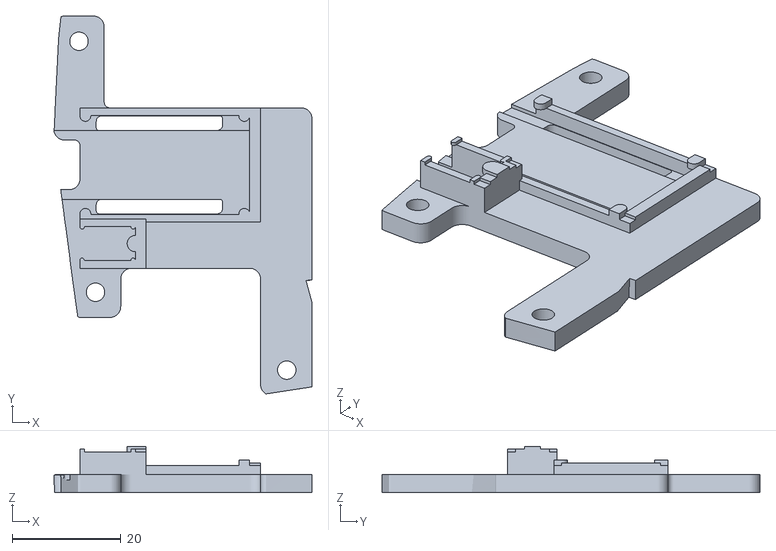
[picture p82: CAD file, 2024-12-28]
v2/cosmotylmt3v1-holderright.stl
47.5 x 69.6 x 8.50
