twalker/3x5_tractyl/case/trackball_holder.step

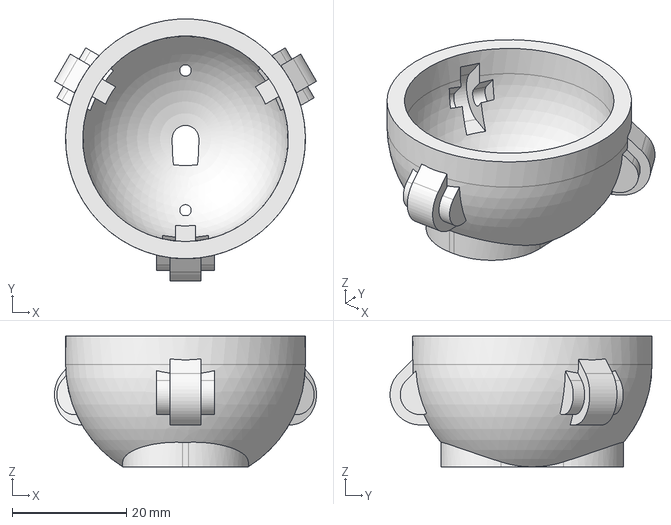
[picture p83: CAD file, 2024-06-30]
case/trackball_holder.step
45.9 x 45.9 x 22.9 mm
