twalker/3x5_tractyl/v2/cosmoskreedes_v1.3mf

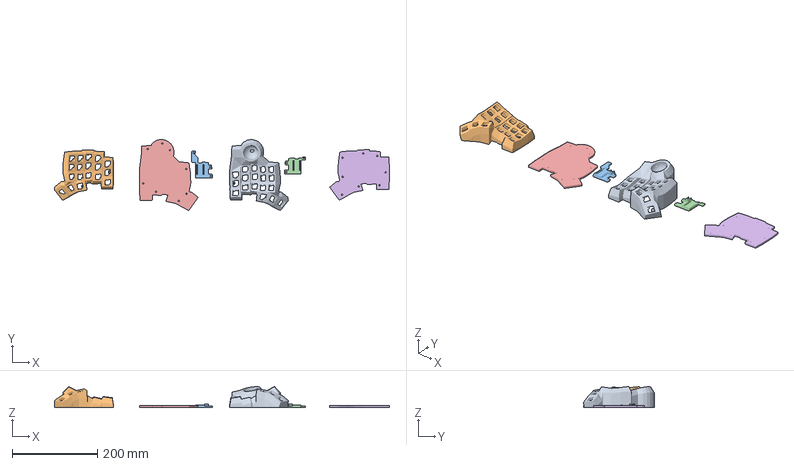
[picture p84: CAD file, 2024-12-28]
v2/cosmoskreedes_v1.3mf
788.2 x 167.3 x 49.4 mm
cosmoskreedes_v1-caseleft.stl
cosmoskreedes_v1-caseright.stl
cosmoskreedes_v1-holderleft.stl
cosmoskreedes_v1-holderright.stl
cosmoskreedes_v1-plateleft.stl
cosmoskreedes_v1-plateright.stl
