twalker/3x5_tractyl/case/lowprocosmotyl2-noweb-wristrest-left.stl

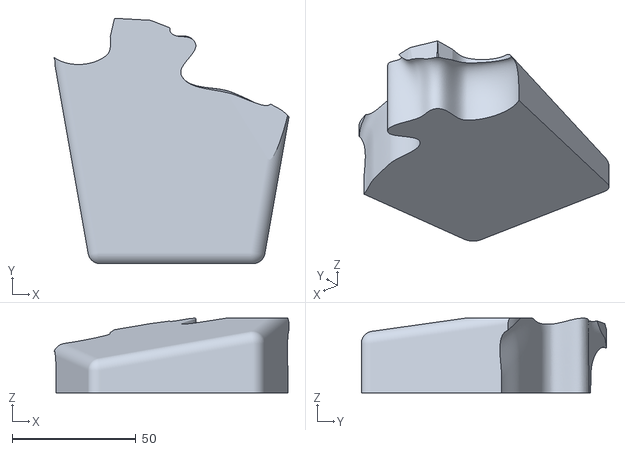
[picture p85: CAD file, 2024-06-30]
case/lowprocosmotyl2-noweb-wristrest-left.stl
94.8 x 99.1 x 30.2
