twalker/3x5_tractyl/v2/cosmoskreedes_v1-caseright.stl

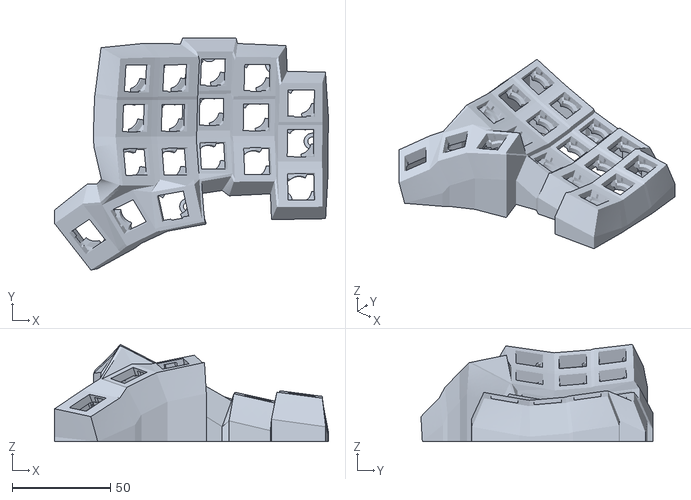
[picture p86: CAD file, 2024-12-28]
v2/cosmoskreedes_v1-caseright.stl
139.2 x 118.0 x 49.4
