twalker/3x5_tractyl/case/pro-micro-holders.3mf

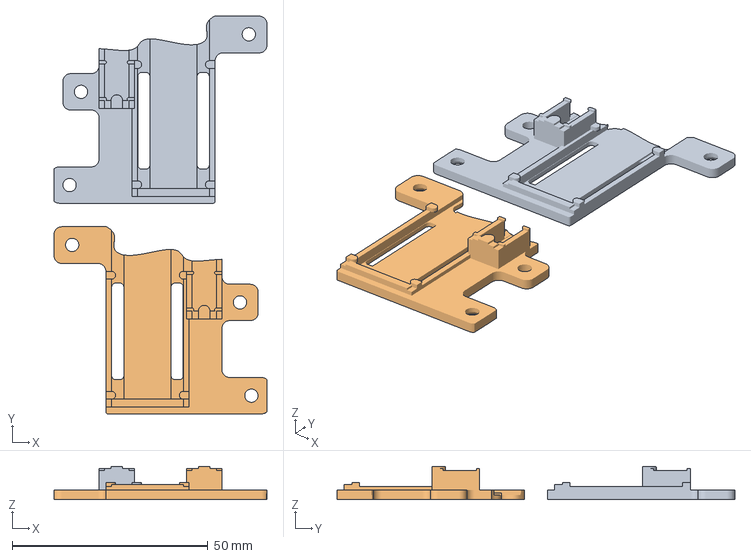
[picture p87: CAD file, 2024-06-30]
case/pro-micro-holders.3mf
54.5 x 101.7 x 8.50 mm
lowprocosmotyl2-noweb3-holder-right.stl
lowprocosmotyl2-noweb3-holder-left.stl
