twalker/3x5_tractyl/case/PMW3360 v12 v1.step

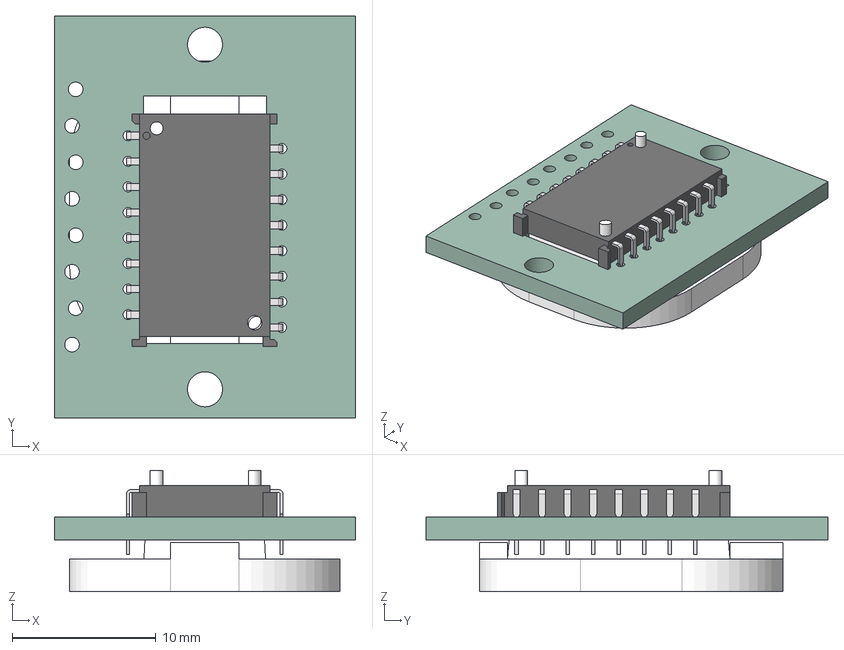
[picture p88: CAD file, 2024-06-30]
case/PMW3360 v12 v1.step
21.0 x 28.0 x 8.46 mm
Lead x 8
Lead(Mirror) x 8
Lens
PMW3360DM PCB
