twalker/3x5_tractyl/case/Mount Plate Test.step

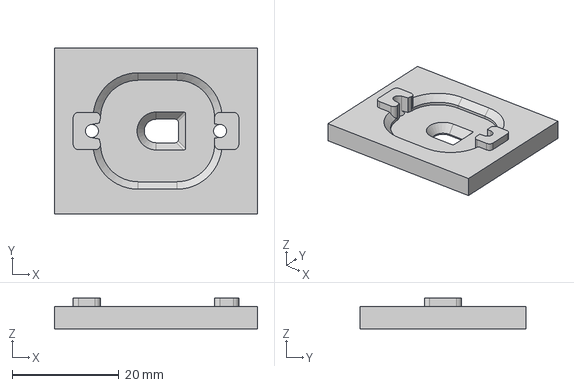
[picture p89: CAD file, 2024-06-30]
case/Mount Plate Test.step
38.0 x 31.0 x 5.80 mm
