twalker/3x5_tractyl/case/cosmotyl4-right.3mf

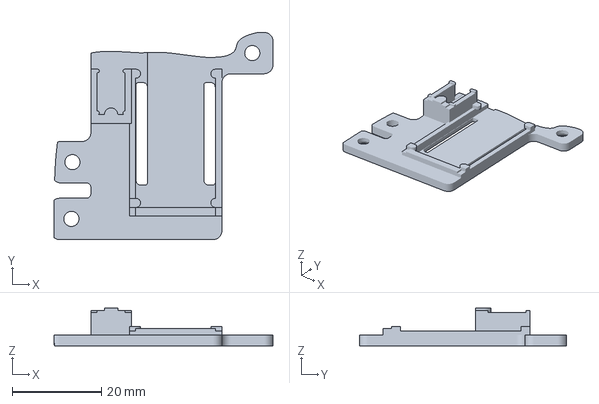
[picture p90: CAD file, 2024-05-17]
case/cosmotyl4-right.3mf
49.2 x 46.5 x 8.50 mm
