twalker/3x5_tractyl/luca/luca_v1.2left.step

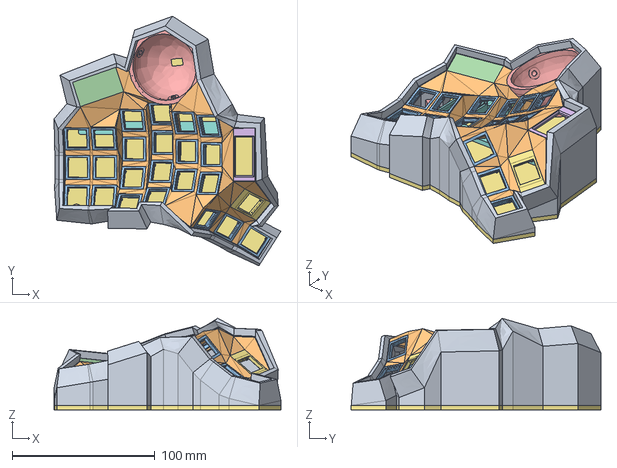
[picture p91: CAD file, 2026-05-09]
luca/luca_v1.2left.step
159.2 x 175.0 x 64.2 mm
