twalker/3x5_tractyl/case/cosmotyl4-wristrests.3mf

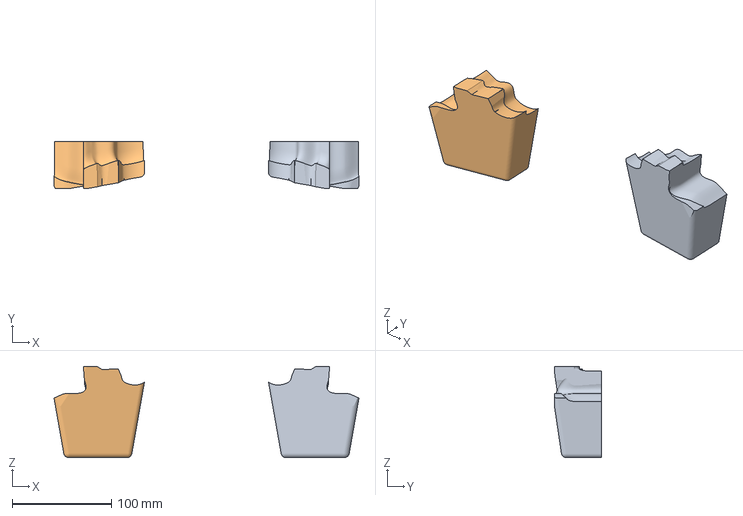
[picture p92: CAD file, 2024-05-17]
case/cosmotyl4-wristrests.3mf
307.2 x 47.5 x 91.9 mm
cosmotyl4-wristrest-left.stl
cosmotyl4-wristrest-right.stl
