twalker/3x5_tractyl/case/cosmotyl4-left.3mf

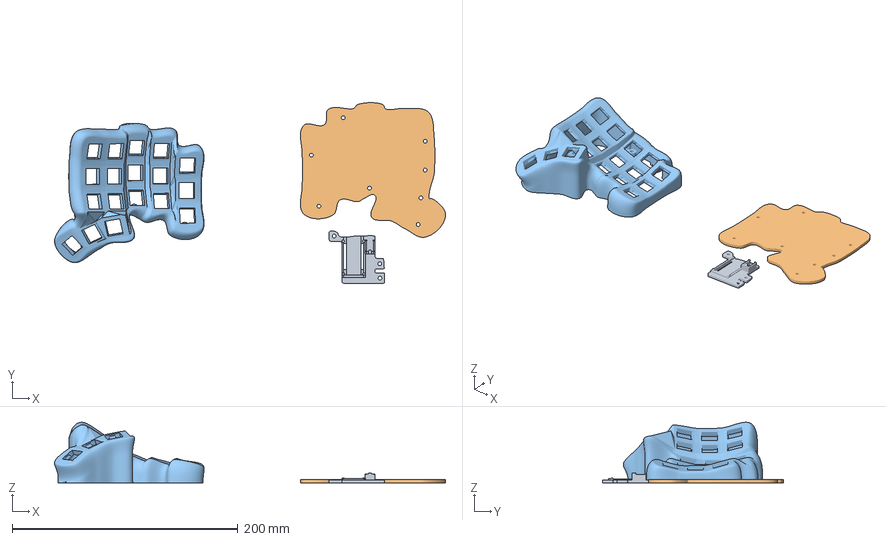
[picture p93: CAD file, 2024-05-17]
case/cosmotyl4-left.3mf
346.6 x 160.2 x 53.7 mm
cosmotyl4-holder-left.stl
cosmotyl4-plate-left.stl
cosmotyl4-case-right.stl
