twalker/3x5_tractyl/case/cosmotyl4-wristrest-left.stl

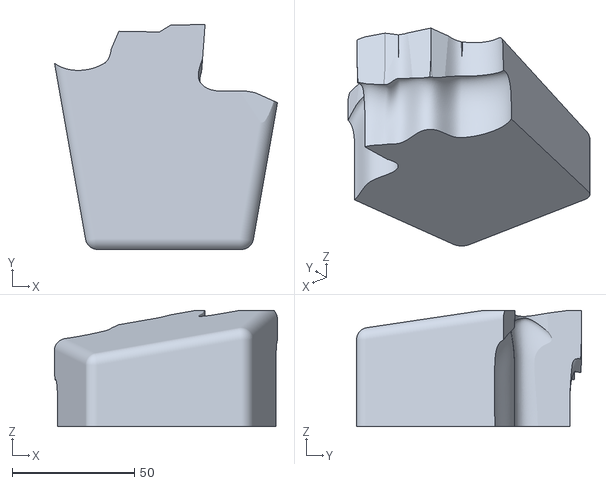
[picture p94: CAD file, 2024-05-12]
case/cosmotyl4-wristrest-left.stl
91.2 x 91.9 x 47.5
