twalker/3x5_tractyl/case/cosmotyl4-plate-right.stl

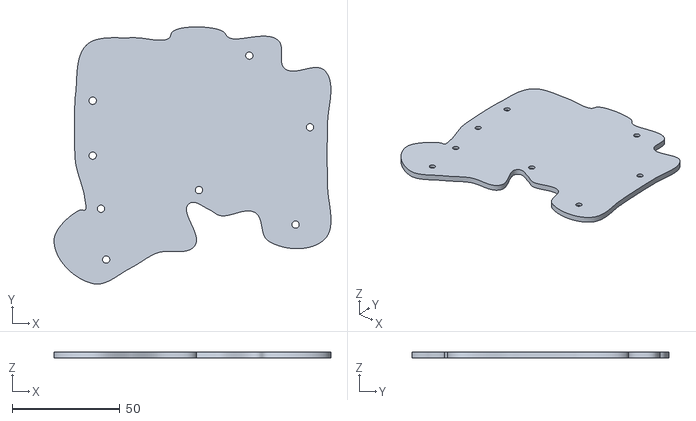
[picture p95: CAD file, 2024-05-12]
case/cosmotyl4-plate-right.stl
128.7 x 119.4 x 3.00
