twalker/3x5_tractyl/luca/luca_v2-caseleft.stl

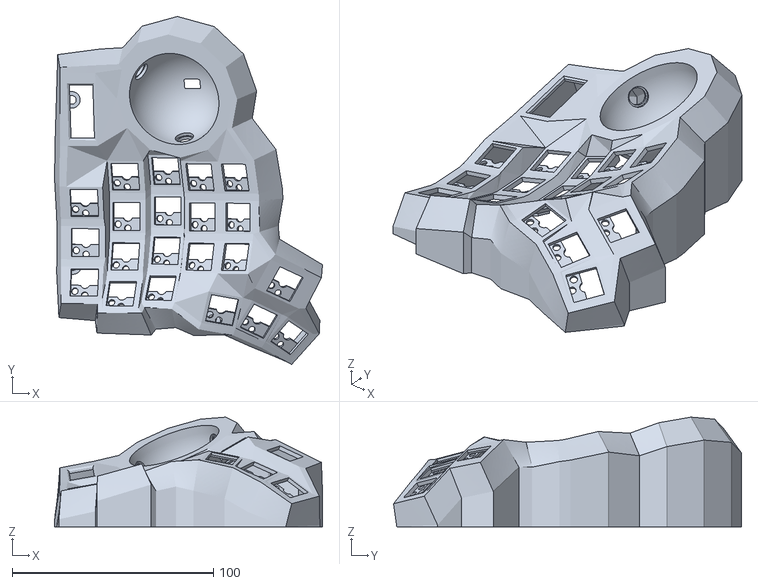
[picture p96: CAD file, 2026-05-09]
luca/luca_v2-caseleft.stl
133.0 x 172.8 x 54.5
