twalker/3x5_tractyl/luca/luca_v2-holderleft.stl

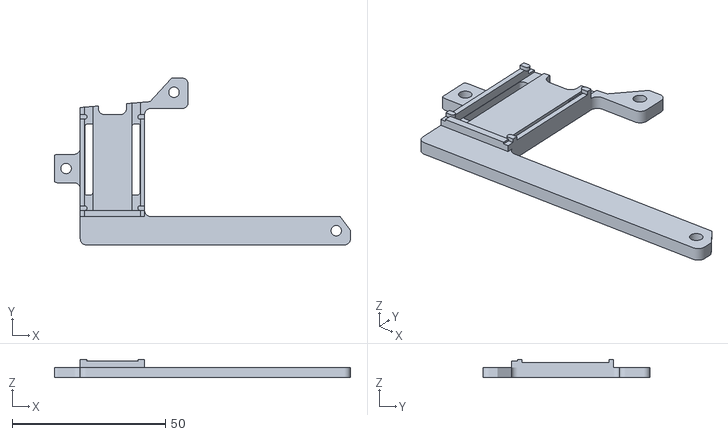
[picture p97: CAD file, 2026-05-09]
luca/luca_v2-holderleft.stl
96.6 x 54.5 x 5.97
