twalker/3x5_tractyl/case/cosmotly4.3mf

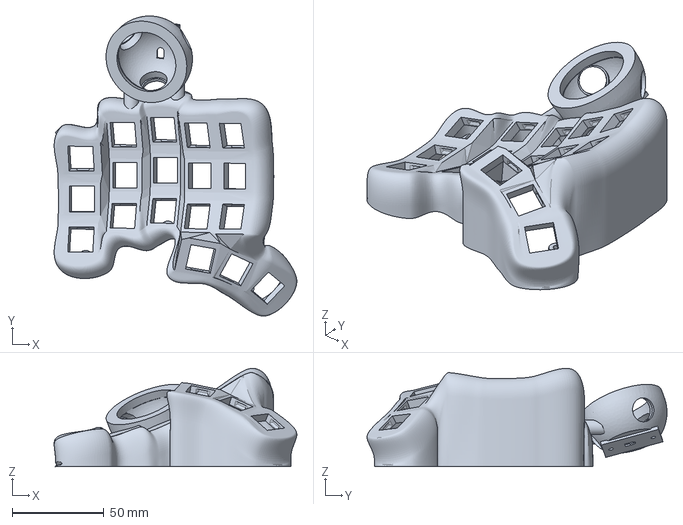
[picture p98: CAD file, 2024-05-12]
case/cosmotly4.3mf
132.6 x 163.9 x 53.7 mm
