twalker/3x5_tractyl/case/phat_btu_socket_w_access.stl

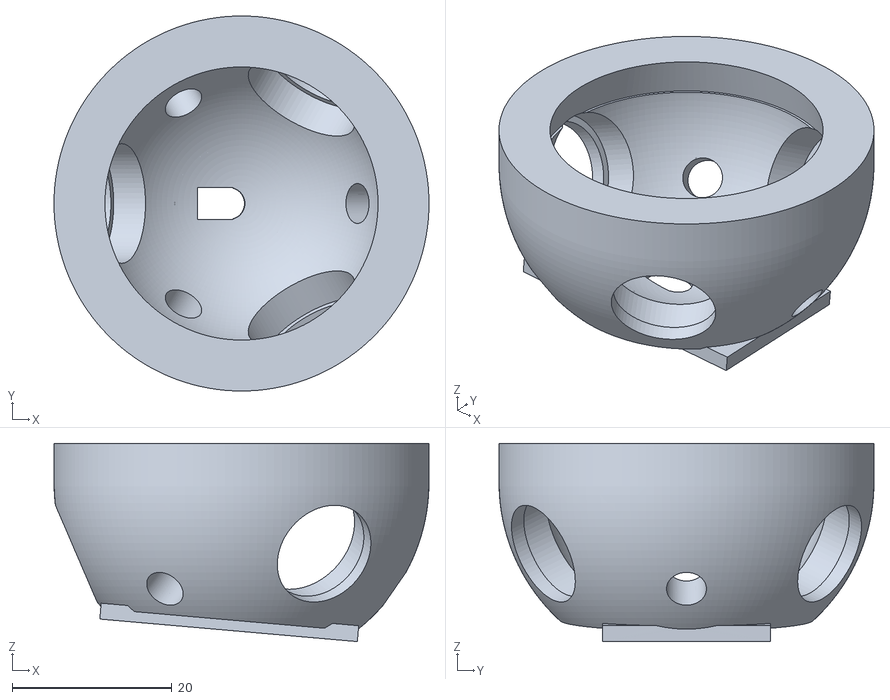
[picture p99: CAD file, 2024-05-09]
case/phat_btu_socket_w_access.stl
47.0 x 47.0 x 24.8
