twalker/3x5_tractyl/case/external_elite_c_trrs_x_2.stl

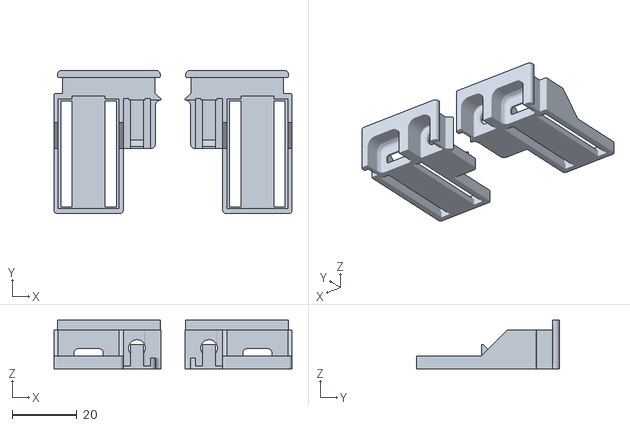
[picture p100: CAD file, 2024-05-09]
case/external_elite_c_trrs_x_2.stl
73.3 x 44.1 x 15.0
