twalker/3x5_tractyl/case/sensor_holder.step

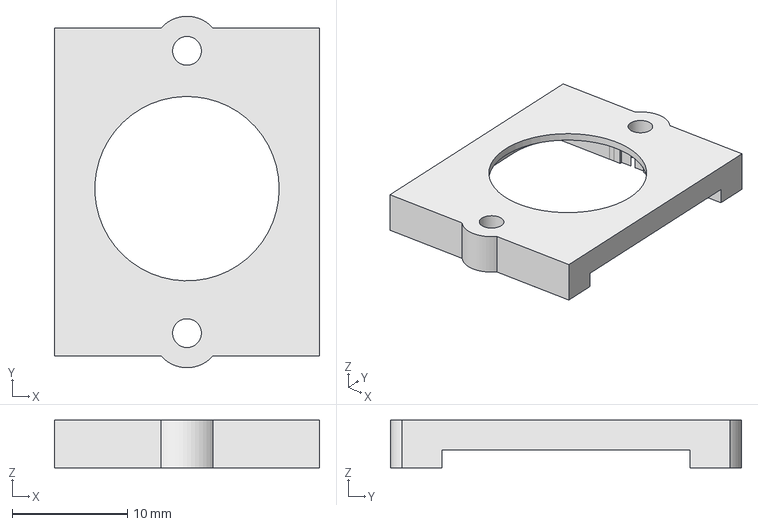
[picture p101: CAD file, 2024-05-09]
case/sensor_holder.step
23.0 x 30.5 x 4.15 mm
