twalker/3x5_tractyl/case/phat_btu_socket.3mf

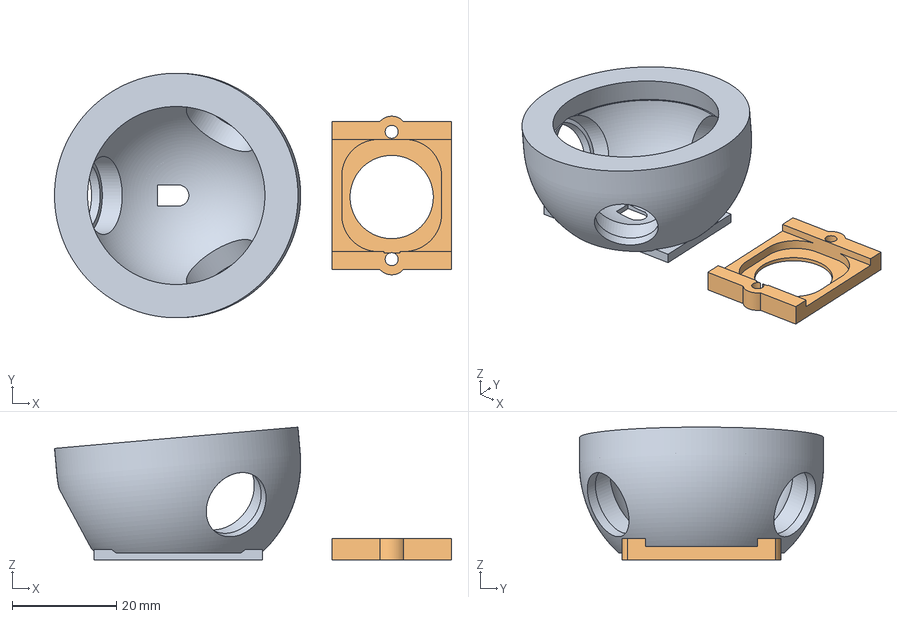
[picture p102: CAD file, 2024-05-09]
case/phat_btu_socket.3mf
76.3 x 47.0 x 25.5 mm
phat_btu_socket.stl
sensor_holder.stl
