twalker/3x5_tractyl/luca/luca_v1.2right.step

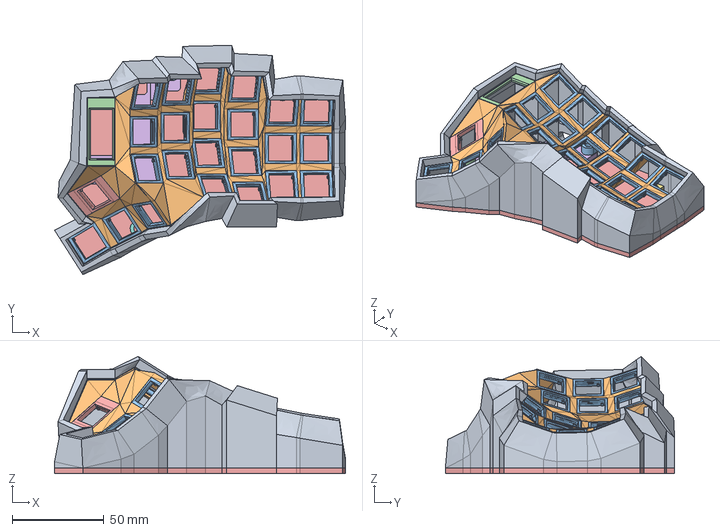
[picture p103: CAD file, 2026-05-09]
luca/luca_v1.2right.step
158.7 x 125.0 x 63.9 mm
