twalker/3x5_tractyl/luca/luca_v2.3mf

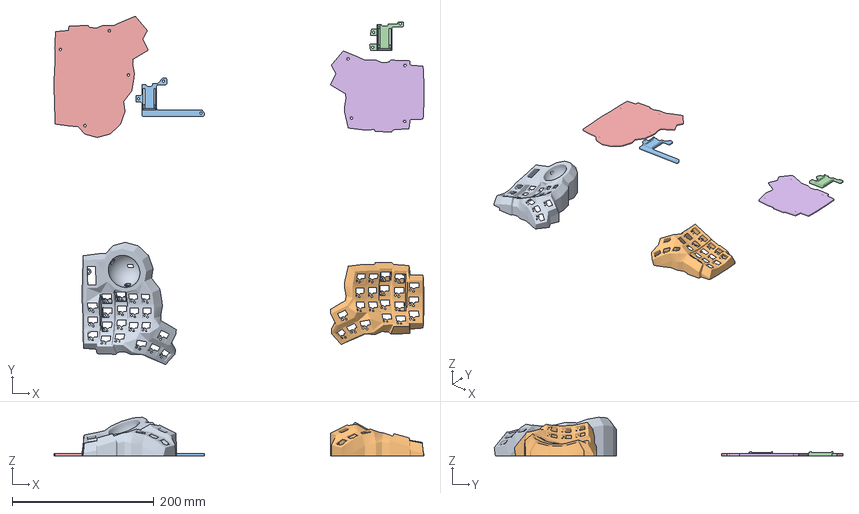
[picture p104: CAD file, 2026-05-09]
luca/luca_v2.3mf
522.0 x 491.7 x 54.5 mm
luca_v2-caseleft.stl
luca_v2-caseright.stl
luca_v2-holderleft.stl
luca_v2-holderright.stl
luca_v2-plateleft.stl
luca_v2-plateright.stl
