twalker/3x5_tractyl/luca/luca_v2-caseright.stl

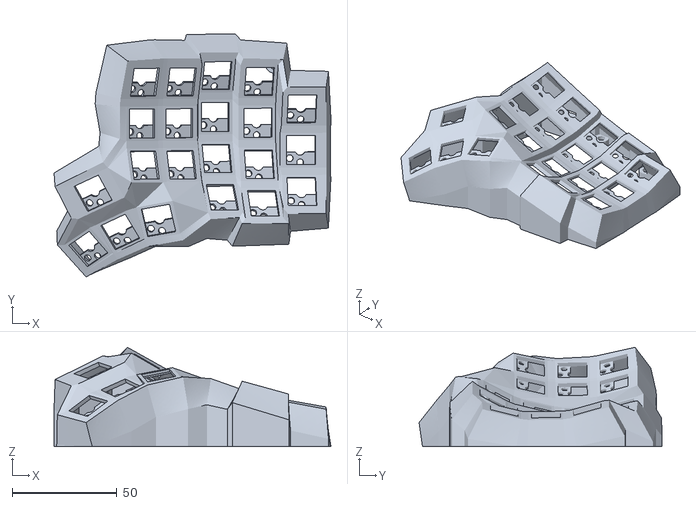
[picture p105: CAD file, 2026-05-09]
luca/luca_v2-caseright.stl
132.1 x 115.8 x 47.4
