twalker/3x5_tractyl/luca/luca_v1.1left.step

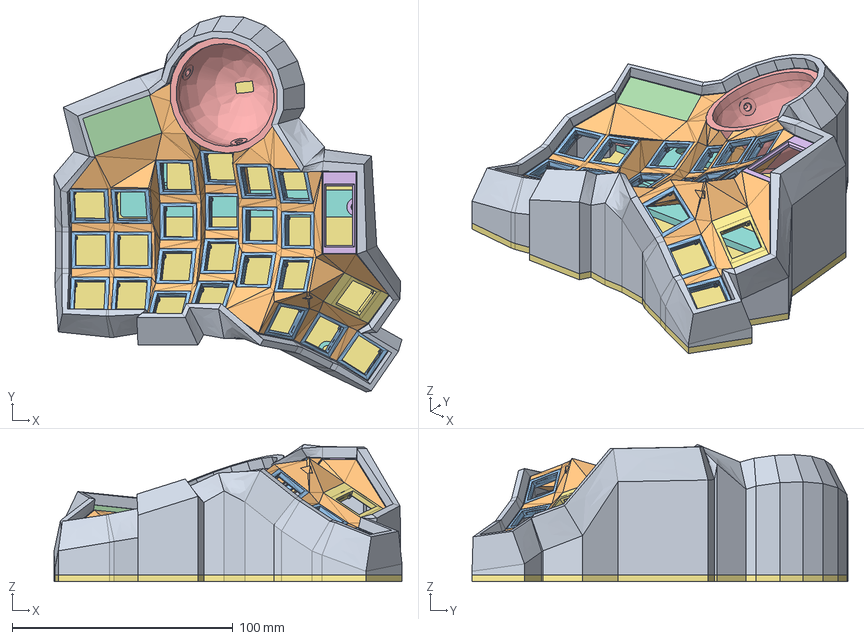
[picture p106: CAD file, 2026-05-09]
luca/luca_v1.1left.step
157.7 x 170.3 x 62.1 mm
