twalker/3x5_tractyl/luca/luca_v1.1right.step

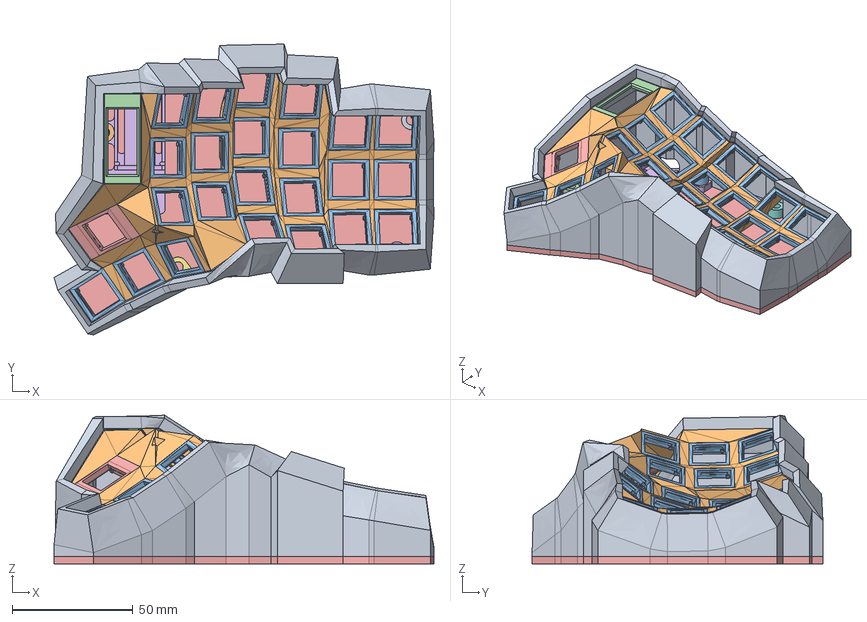
[picture p107: CAD file, 2026-05-09]
luca/luca_v1.1right.step
157.2 x 120.3 x 61.5 mm
