twalker/3x5_tractyl/case/Les Finestres_Print_Enhanced-low_res-scale-2_00x.webp

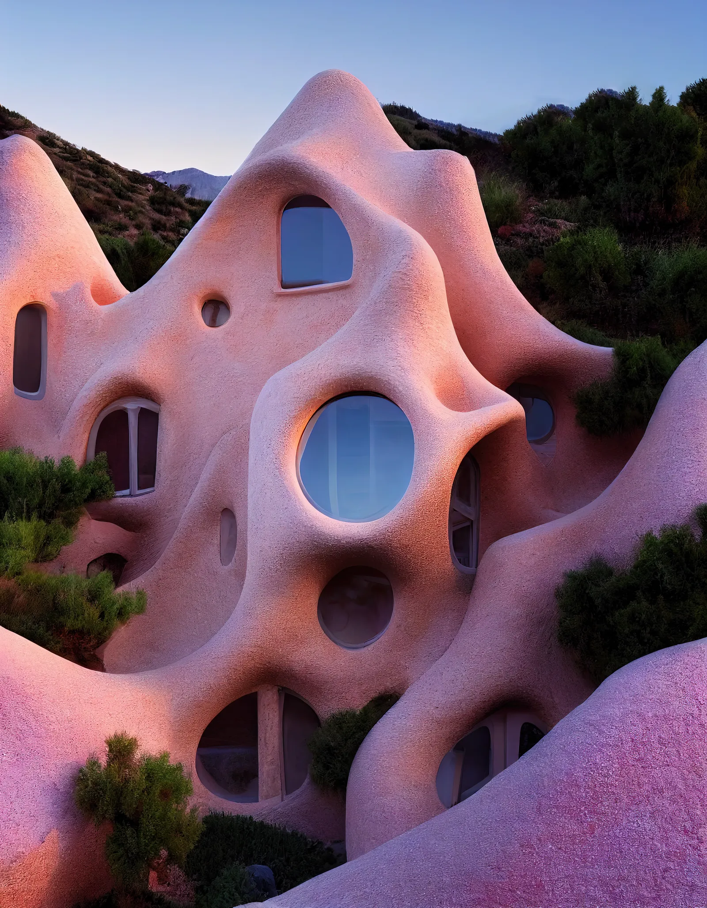
case/Les Finestres_Print_Enhanced-low_res-scale-2_00x.webp
