twalker/3x5_tractyl/wiring-diagram/3x5_tractyl-Left.png

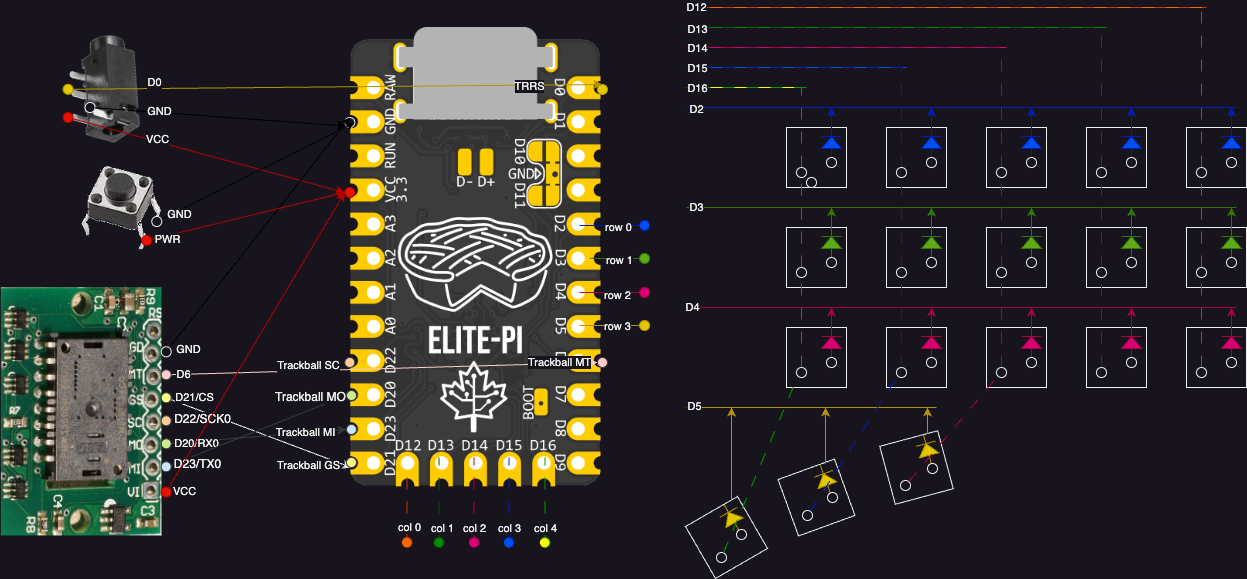
wiring-diagram/3x5_tractyl-Left.png
