twalker/3x5_tractyl/wiring-diagram/3x5_tractyl-Right.png

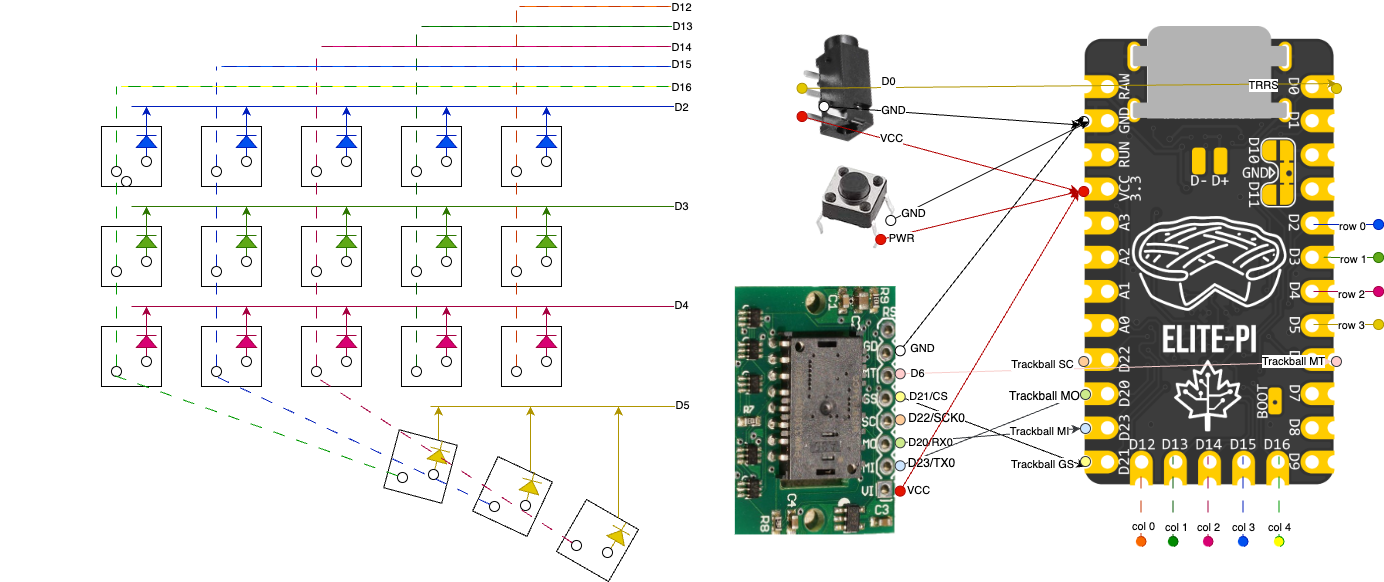
wiring-diagram/3x5_tractyl-Right.png
