twalker/3x5_tractyl/wiring-diagram/3x5_tractyl.png

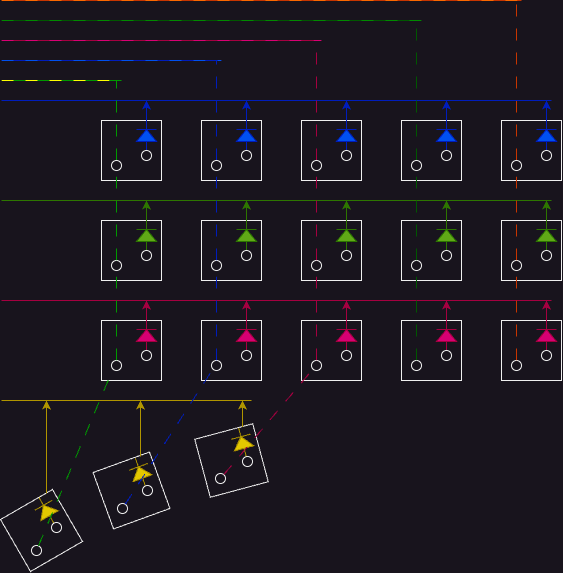
wiring-diagram/3x5_tractyl.png
