twalker/3x5_tractyl/wiring-diagram/battery.png

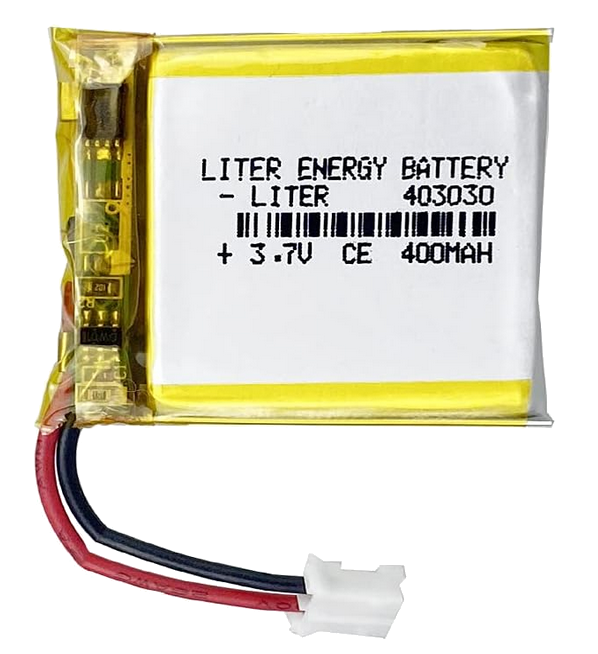
wiring-diagram/battery.png
