twalker/3x5_tractyl/wiring-diagram/core-wiring-pinout.png

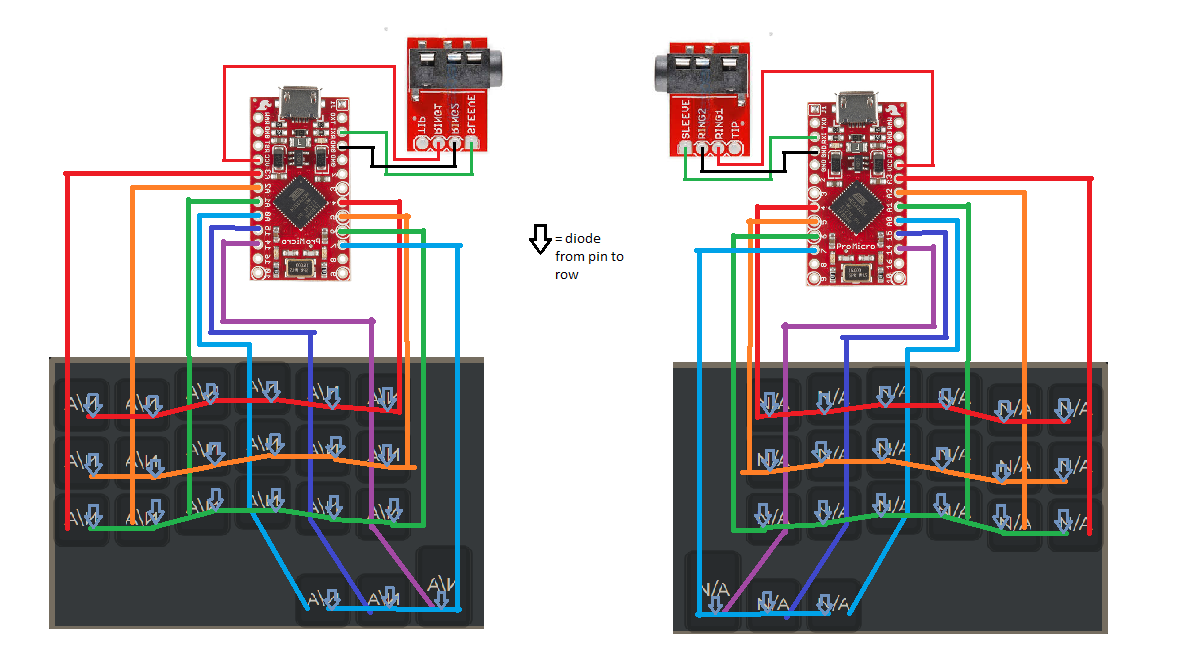
wiring-diagram/core-wiring-pinout.png
