twalker/3x5_tractyl/wiring-diagram/elite-c-back-cleaned.png

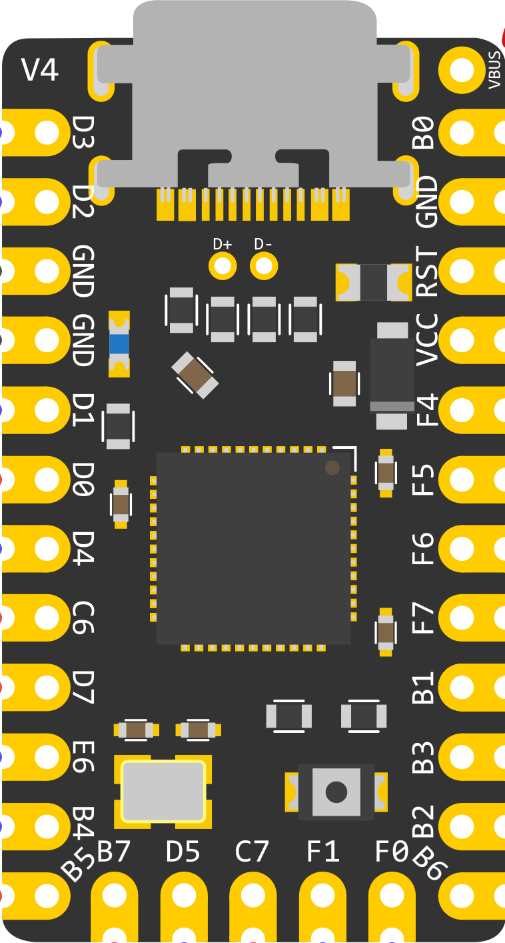
wiring-diagram/elite-c-back-cleaned.png
