twalker/3x5_tractyl/wiring-diagram/elite-c-back.png

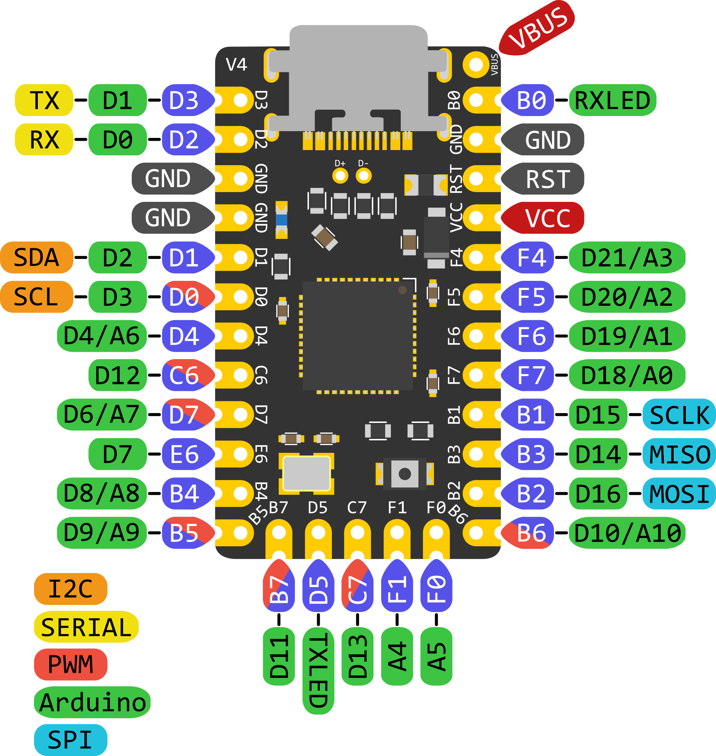
wiring-diagram/elite-c-back.png
