twalker/3x5_tractyl/wiring-diagram/pmw3360.jpg

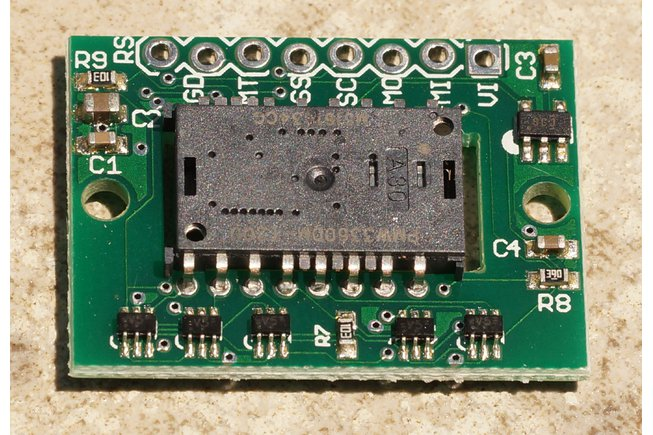
wiring-diagram/pmw3360.jpg
