twalker/3x5_tractyl/wiring-diagram/pmw3389.jpg

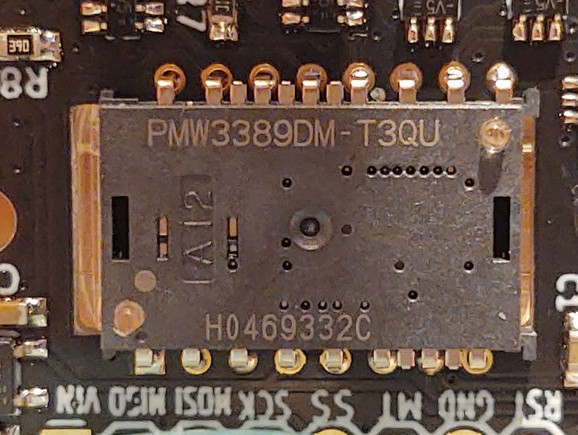
wiring-diagram/pmw3389.jpg
