twalker/3x5_tractyl/wiring-diagram/pmw3389_cleaned.jpg

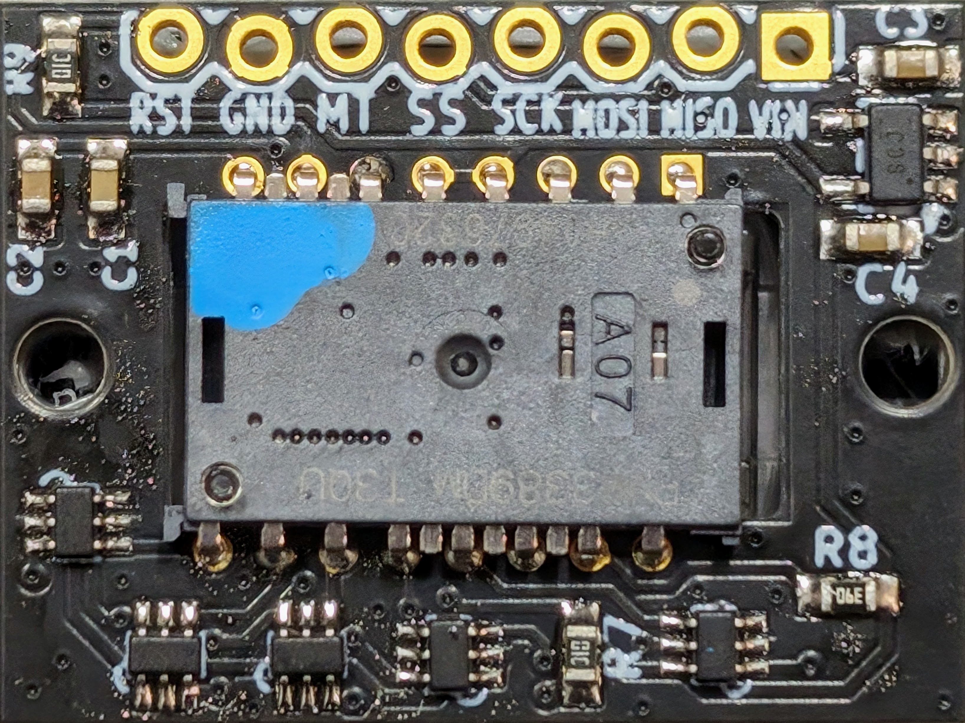
wiring-diagram/pmw3389_cleaned.jpg
