twalker/3x5_tractyl/wiring-diagram/pmw3610.jpg

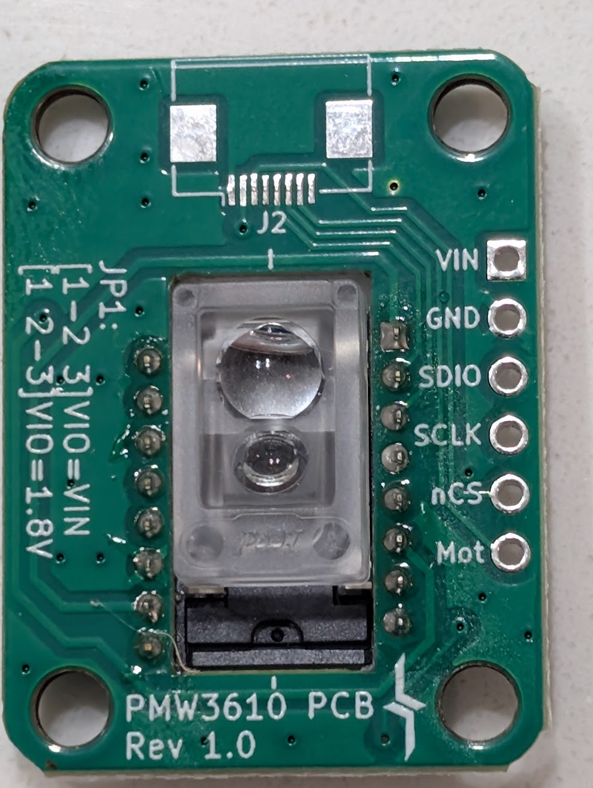
wiring-diagram/pmw3610.jpg
