twalker/3x5_tractyl/wiring-diagram/pmw-3610_cleaned.jpg

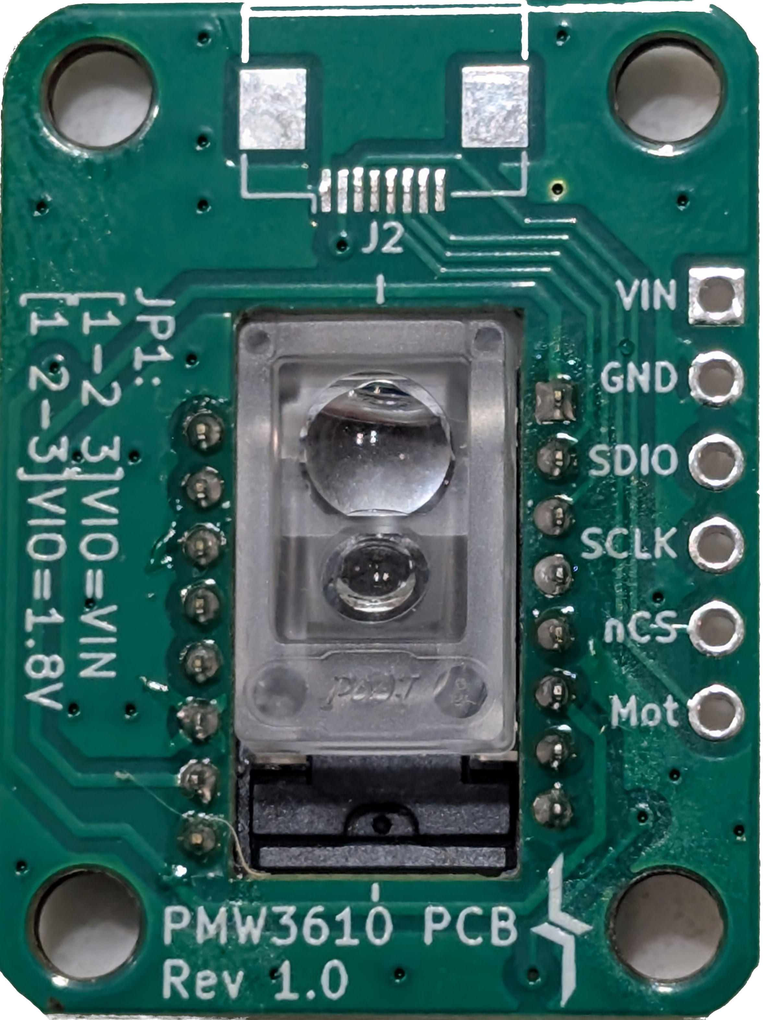
wiring-diagram/pmw-3610_cleaned.jpg
