twalker/3x5_tractyl/wiring-diagram/power-switch.png

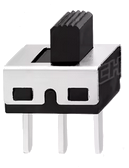
wiring-diagram/power-switch.png
