twalker/3x5_tractyl/wiring-diagram/reset.png

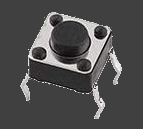
wiring-diagram/reset.png
