twalker/3x5_tractyl/wiring-diagram/review-rp2040-pro-micro-split-keyboard-winsplit-v0-vyr30ogq61sc1.webp

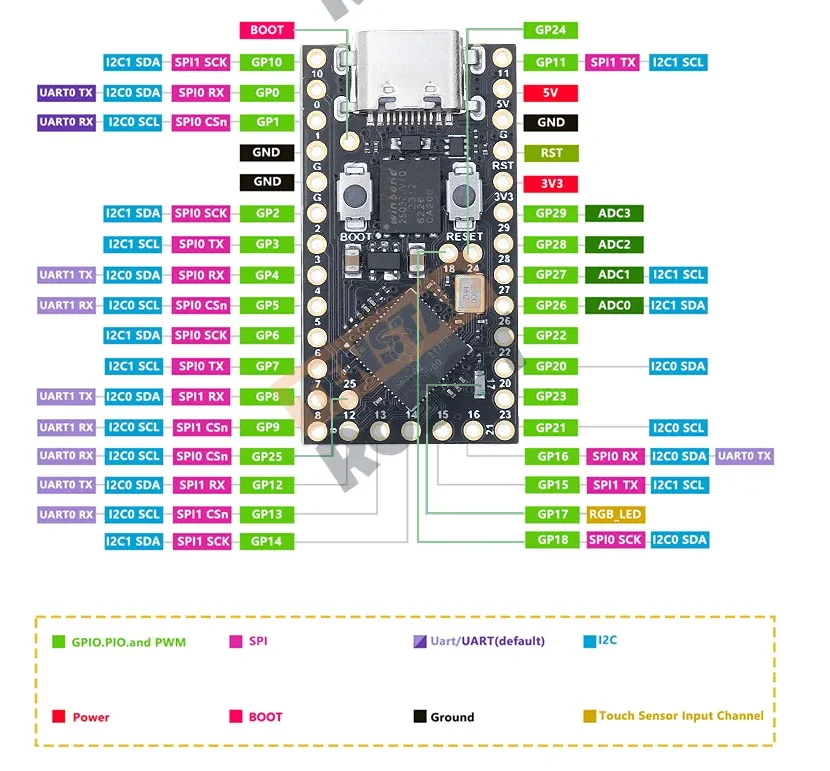
wiring-diagram/review-rp2040-pro-micro-split-keyboard-winsplit-v0-vyr30ogq61sc1.webp
