twalker/3x5_tractyl/wiring-diagram/trrs2.jpg

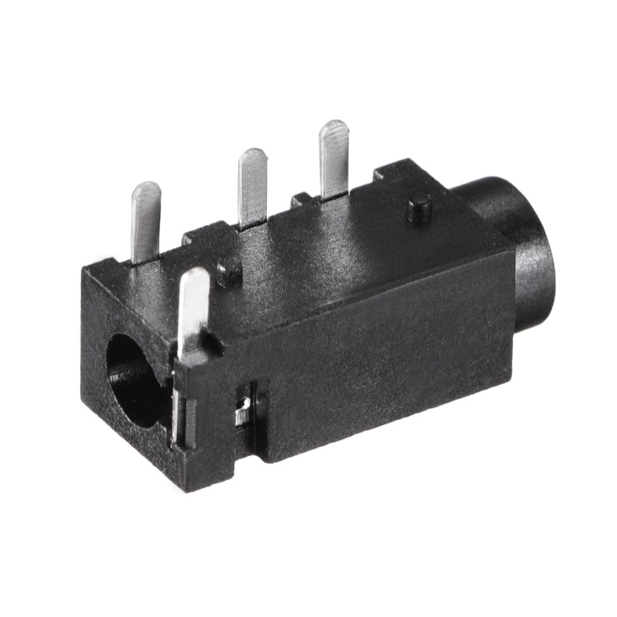
wiring-diagram/trrs2.jpg
