twalker/3x5_tractyl/wiring-diagram/trrsjack.jpg

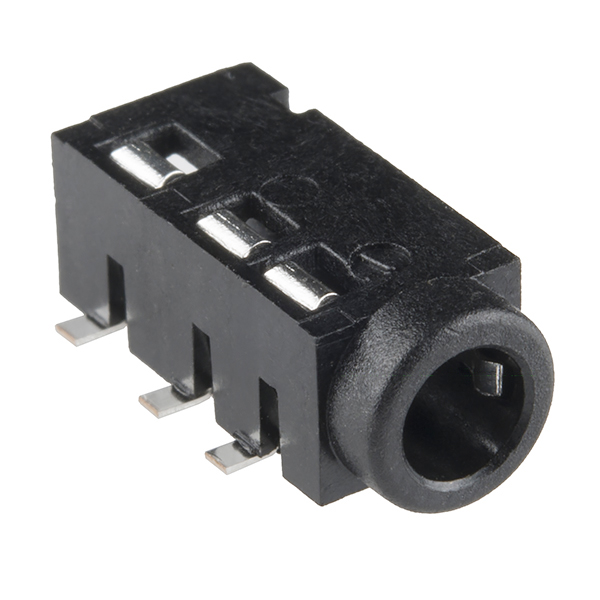
wiring-diagram/trrsjack.jpg
